MMBytes/MultiGeiger-V2/main/http_server.c

#include "http_server.h"

#include <stdlib.h>
#include <string.h>
#include <stdio.h>
#include <stdarg.h>
#include <time.h>
#include "esp_http_server.h"
#include "esp_log.h"
#include "esp_ota_ops.h"
#include "esp_partition.h"
#include "esp_chip_info.h"     // V2.3.13: chip-model lookup for OTA target validation
#include "esp_app_format.h"    // V2.3.13: ESP_CHIP_ID_* constants for OTA validation
#include "esp_app_desc.h"
#include "esp_flash.h"
#include "esp_heap_caps.h"
#include "esp_system.h"
#include "esp_timer.h"
#include "esp_wifi.h"
#include "esp_mac.h"
#include "esp_netif.h"
#include "esp_sntp.h"
#include "lwip/ip4_addr.h"
#include "lwip/sockets.h"
#include "lwip/inet.h"
#include "mbedtls/base64.h"
#include "esp_tls_errors.h"   // V2.8.0: ESP_TLS_ERR_SSL_WANT_READ/_WRITE — how
                              // a TLS recv timeout reaches update_post

#include "version.h"
#include "applog.h"
#include "diag.h"              // V2.4.32: diag_log_heap (net-RAM split at OTA-prep)
#include "coredump.h"          // V2.4.18: panic dump availability + summary + /coredump.elf
#include "hal.h"
#if HAL_HAS_PSRAM
#include "esp_psram.h"         // V2.8.2: esp_psram_get_size — the /status Memory line was a literal "8 MB"
#endif
#include "pm_sensor.h"
#include "env_sensor.h"
#include "noise_sensor.h"
#include "sgp41.h"             // V2.6.15: SGP41 VOC+NOx sensor (NOx index only)
#include "display.h"           // V2.3.30: live-apply OLED brightness via display_set_contrast
#include "als.h"               // V2.3.29: ambient light sensor (FeatherS3-D)
#include "veml7700.h"          // V2.3.30: I²C ambient light sensor (any board)
#include "fuel_gauge.h"        // V2.6.6: MAX17048 battery fuel gauge (FeatherS3-D)
#include "gnss.h"              // V2.5.8: I²C GNSS receiver (PA1010D / MAX-M10S)
#include "sd_logger.h"         // V2.6.19: standalone-mode CSV logger status (/status card)
#include "tube.h"
#include "tube_pcnt.h"         // V2.5.16: release PCNT comb DRAM in OTA teardown
#include "speaker.h"           // V2.7.5: silence the pulse tick in OTA teardown
#include "history.h"            // V2.5.6: CPM history for the /status graph
#include "transmission.h"
#include "log_ftp.h"
#include "main_status.h"       // V2.4.1 (A4): consolidated status snapshot
#include "mqtt.h"              // V2.4.4: MQTT connection state for /status row
#include "syslog.h"            // V2.4.15: tear down UDP socket in OTA teardown
#include "sysinfo.h"           // V2.4.26: reset_reason_str / chip_model_str (also used by mqtt.c)
#include "ntp.h"               // ntp_time_valid — the clock-sane gate
#include "util.h"              // V2.4.1+ (T1): ct_memcmp, html_esc, url_decode, safe_strcpy
#include "env_api.h"           // V2.7.3: /api/env wire contract (format + parse)
#include "lorawan.h"           // V2.6.23 (T8): lorawan_get_status()/_state_name()/_region_name()
                               // for /status; no-op stubs on the ten non-V4-R2 boards (see
                               // lorawan.h) so this include is unconditional like gnss.h/sgp41.h.
#include "tls_cert.h"          // V2.8.0: PEM pointers + fingerprint for HTTPS
#include "tls_logic.h"         // V2.8.0: https_redirect_location (Task 5)
#include "freertos/task.h"     // V2.8.0: uxTaskGetStackHighWaterMark — httpd stack headroom on /
#if HAL_HAS_HTTPS
#include "esp_https_server.h"  // V2.8.0: httpd_ssl_start — same httpd underneath, TLS on top
#endif
#if HAL_HAS_LORAWAN
#include "lorawan_codec.h"     // V2.6.23 (T8): lw_hex_decode() — /config POST EUI/key length
                               // validation, V4-R2 only. Ringfenced per the brief: other boards
                               // must not gain even this glue.
#endif

static const char *TAG = "http";

static httpd_handle_t s_server   = NULL;
#if HAL_HAS_HTTPS
// V2.8.0: true once httpd_ssl_start() succeeded on :443. Read by the :80
// instance bring-up (Task 5) and the /status Device card; false means we
// fell back to plain HTTP on :80 and there is nothing to redirect to.
static bool s_https_up = false;
// V2.8.0 (fix wave 5): https_enable as read at http_server_start(), before a
// /config POST can overwrite *s_cfg in place. The transport cannot change
// live, so the /status Device card must describe what THIS boot is doing,
// not a pending edit — read this instead of s_cfg->https_enable there.
static bool s_https_cfg_at_boot = false;
static httpd_handle_t s_redirect = NULL;   // :80 instance, NULL if not running
#endif
static config_t      *s_cfg      = NULL;
static const char    *s_chip_id  = "";
static char           s_mac_str[18] = "??:??:??:??:??:??";   // filled at start
// V2.4.1 (A9): the pre-V2.4.1 `static volatile bool s_restart_requested`
// + `http_server_restart_requested()` polled-flag pair was replaced with
// an event-bit notification — handlers now call main_request_restart()
// from main_status.h, which both sets a persistent flag and wakes the
// main loop's xEventGroupWaitBits via EV_RESTART. Drops "click Save and
// restart" -> reboot latency from up to 1 s to ~µs.

// --- Access log --------------------------------------------------------------
// Logs every incoming request with its URI and client IP. Called at the top of
// every handler, before auth checks, so unauthorised attempts are visible too.

static void peer_ipstr(httpd_req_t *req, char *out, size_t outsz) {
    if (outsz == 0) return;
    out[0] = '?';
    out[1] = 0;
    int sockfd = httpd_req_to_sockfd(req);
    if (sockfd < 0) return;
    struct sockaddr_storage addr;
    socklen_t len = sizeof(addr);
    if (getpeername(sockfd, (struct sockaddr *)&addr, &len) != 0) return;
    if (addr.ss_family == AF_INET) {
        inet_ntop(AF_INET,
                  &((struct sockaddr_in *)&addr)->sin_addr,
                  out, outsz);
    } else if (addr.ss_family == AF_INET6) {
        inet_ntop(AF_INET6,
                  &((struct sockaddr_in6 *)&addr)->sin6_addr,
                  out, outsz);
    }
}

#if HAL_HAS_HTTPS
static void tls_sess_mark_served(int fd);   // defined in the TLS session accounting block below
#endif
static void log_access(httpd_req_t *req, const char *what) {
    char ipstr[48];
    peer_ipstr(req, ipstr, sizeof(ipstr));
    ESP_LOGI(TAG, "%s from %s", what, ipstr);
#if HAL_HAS_HTTPS
    // Only the :443 instance has TLS sessions to account for; the :80
    // handlers share this helper but must not touch the table (single-task
    // rule, see the TLS session accounting block).
    if (req->handle == s_server) tls_sess_mark_served(httpd_req_to_sockfd(req));
#endif
}

#if HAL_HAS_HTTPS
// --- TLS session accounting (V2.8.1) ------------------------------------------
// A browser opens several connections to a new host at once; on this single
// httpd task each TLS handshake is ~1 s of software ECDSA (the S3 has no ECC
// block), so the spares wait their turn, COMPLETE the handshake, and are then
// reset by the client before sending a request (bench + five-node review,
// 2026-09-13; still the case with the CA imported into the browser, so it is
// ordinary speculative pre-connection, not a certificate-error retry).
// esp-tls logs each such first-read reset at ERROR
// ("read error :-0x0050"), two to five per page load, and that tag also
// carries every genuine TLS read/write failure — so it must stay at ERROR.
// Instead, account for sessions here: mark the socket at its first request,
// and at session close report the ones that never carried one at INFO. A
// "read error" that is NOT paired with a "closed before any request" line is
// the real thing.
//
// Both callbacks run on the :443 httpd task, and log_access() marks a
// session only when the request arrived on that instance (req->handle ==
// s_server) — the :80 handlers also call log_access() but never reach the
// table — so every access is from ONE task and it needs no lock.
#define TLS_SESS_SLOTS 8   // > max_open_sockets (5) + the accept in flight
static struct { int fd; bool served; } s_tls_sess[TLS_SESS_SLOTS];

static void tls_sess_mark_served(int fd) {
    for (int i = 0; i < TLS_SESS_SLOTS; i++) {
        if (s_tls_sess[i].fd == fd) { s_tls_sess[i].served = true; return; }
    }
}

static void tls_sess_user_cb(esp_https_server_user_cb_arg_t *arg) {
    int fd = -1;
    if (!arg || !arg->tls || esp_tls_get_conn_sockfd(arg->tls, &fd) != ESP_OK) return;
    switch (arg->user_cb_state) {
    case HTTPD_SSL_USER_CB_SESS_CREATE:
        for (int i = 0; i < TLS_SESS_SLOTS; i++) {
            if (s_tls_sess[i].fd == 0 || s_tls_sess[i].fd == fd) {
                s_tls_sess[i].fd = fd; s_tls_sess[i].served = false; return;
            }
        }
        return;                      // table full: this session goes unaccounted
    case HTTPD_SSL_USER_CB_SESS_ERROR:
        // Handshake never completed. This fires for EVERY failed handshake —
        // a browser hanging up mid-handshake (-0x7280, about once per cold
        // page load), but also a port scan, a plaintext probe on :443, a
        // version mismatch, or the 9 s handshake budget — and the callback
        // cannot tell them apart: httpd_ssl_open clears the esp-tls error
        // record before invoking it. So this line is a marker, not a verdict;
        // the code on the esp-tls line above it says which case. V2.8.2: name
        // the two codes an operator actually meets. The stress test of
        // 2026-09-15 showed a silent client logs
        // "esp_tls_create_server_session failed, 0xffff7ff7" — that is
        // -0x8009 = ESP_ERR_ESP_TLS_SERVER_HANDSHAKE_TIMEOUT, our 9 s
        // tls_handshake_timeout_ms — and the old text still blamed a browser.
        ESP_LOGI(TAG, "TLS handshake on fd %d did not complete — see the esp-tls line above "
                      "(-0x7280 = client hung up, a browser's spare connection; "
                      "0xffff7ff7 = the 9 s handshake budget, a client that never spoke)", fd);
        return;
    case HTTPD_SSL_USER_CB_SESS_CLOSE:
        for (int i = 0; i < TLS_SESS_SLOTS; i++) {
            if (s_tls_sess[i].fd == fd) {
                if (!s_tls_sess[i].served) {
                    ESP_LOGI(TAG, "TLS session on fd %d closed before any request "
                                  "(a browser's abandoned parallel connection — harmless)", fd);
                }
                s_tls_sess[i].fd = 0;
                return;
            }
        }
        return;
    default:
        return;
    }
}
#endif  // HAL_HAS_HTTPS

// --- Auth --------------------------------------------------------------------

// V2.4.1+ (T1): ct_memcmp moved to util.h as a static inline so the host-
// side test runner under `test/` can include it directly. Same constant-
// time semantics as the V2.3.33 (B2) original.

// Returns true if Authorization header is "Basic base64(admin:<ap_password>)".
// On failure, sends 401 + WWW-Authenticate and returns false. The caller must
// return ESP_OK immediately without sending anything further.
//
// Distinguishes two failure modes: header absent (expected first-touch from
// a fresh browser — logged as INFO) vs. header present but wrong credentials
// (a real bad-password attempt — logged as WARN so it stands out in /log).
static bool check_auth(httpd_req_t *req) {
    char header[160];
    size_t hlen = httpd_req_get_hdr_value_len(req, "Authorization");
    bool header_present = (hlen > 0 && hlen < sizeof(header));
    if (!header_present) goto unauth;
    if (httpd_req_get_hdr_value_str(req, "Authorization", header, sizeof(header)) != ESP_OK) {
        goto unauth;
    }
    if (strncmp(header, "Basic ", 6) != 0) goto unauth;

    char userpass[128];
    int n = snprintf(userpass, sizeof(userpass), "admin:%s", s_cfg->ap_password);
    if (n <= 0 || (size_t)n >= sizeof(userpass)) goto unauth;

    unsigned char expected[200];
    size_t enc_len = 0;
    if (mbedtls_base64_encode(expected, sizeof(expected) - 1, &enc_len,
                              (const unsigned char *)userpass, strlen(userpass)) != 0) {
        goto unauth;
    }
    expected[enc_len] = 0;
    // V2.3.33: length check first, then constant-time byte compare. Length
    // mismatch is non-secret (derivable from the credential layout) so the
    // early exit is fine; the byte comparison must be timing-safe.
    size_t got_len = strlen(header + 6);
    if (got_len != enc_len) goto unauth;
    if (ct_memcmp(header + 6, expected, enc_len) != 0) goto unauth;
    return true;

unauth:
    if (header_present) {
        char ipstr[48];
        peer_ipstr(req, ipstr, sizeof(ipstr));
        ESP_LOGW(TAG, "auth failed for %s from %s", req->uri, ipstr);
    }
    httpd_resp_set_status(req, "401 Unauthorized");
    httpd_resp_set_hdr(req, "WWW-Authenticate", "Basic realm=\"MultiGeiger\"");
    httpd_resp_send(req, NULL, 0);
    return false;
}

// --- CSRF guard for state-changing POST handlers ----------------------------
//
// V2.3.33: defends against cross-site request forgery on /config, /update,
// /reboot. Basic-auth credentials are cached per-origin by browsers and
// auto-attached to any subsequent request to the same origin — including
// cross-origin form POSTs from a malicious page the admin happens to visit
// in the same browser session. Without this guard, an attacker page can
// `<form action="http://device/config" method=POST>` with arbitrary fields,
// the browser attaches the cached Authorization header, and the request
// succeeds silently.
//
// Defence: require the request's Origin header to match this server's scheme
// AND Host (preferred — all modern browsers set Origin on cross-origin POST
// and on most same-origin POSTs); fall back to Referer, matched the same way
// on its host prefix. If neither header is present, deny — programmatic
// clients (curl, scripts) can pass `-H "Origin: http://<device>:<port>"`, or
// `-H "Origin: https://<device>"` on an HTTPS node, to satisfy the check.
//
// V2.8.0 (fix wave 7): the scheme is part of the comparison, not stripped and
// ignored. An origin is scheme+host+port, and with :80 still open (redirector,
// no HSTS) an attacker who answers port 80 — or spoofs it on the LAN — can
// serve a page from `http://<device>` whose form POSTs to `https://<device>`;
// a host-only check would call that same-origin, and the browser attaches the
// Basic credential it cached for :443. Binding the scheme the main server
// actually runs on closes that path.
//
// Caller must `return ESP_OK` immediately when this returns false.
static bool check_same_origin(httpd_req_t *req) {
    char host[64];
    if (httpd_req_get_hdr_value_str(req, "Host", host, sizeof(host)) != ESP_OK) {
        goto deny;
    }
    size_t host_len = strlen(host);
    // The transport this handler is reachable on. Protected POSTs only ever
    // land on the main instance: the :80 instance serves only /cert.pem, /log
    // and /api/env (none protected) plus the 301 wildcard, so there is no
    // mixed case to consider here.
#if HAL_HAS_HTTPS
    const char *scheme = s_https_up ? "https://" : "http://";
#else
    const char *scheme = "http://";
#endif
    size_t scheme_len = strlen(scheme);

    char origin[128];
    if (httpd_req_get_hdr_value_str(req, "Origin", origin, sizeof(origin)) == ESP_OK) {
        // Origin format: "scheme://host[:port]" with no path. The scheme must
        // be ours, and what follows it must equal Host exactly.
        if (strncmp(origin, scheme, scheme_len) != 0) goto deny;
        if (strcmp(origin + scheme_len, host) == 0) return true;
        goto deny;
    }

    char referer[160];
    if (httpd_req_get_hdr_value_str(req, "Referer", referer, sizeof(referer)) == ESP_OK) {
        // Referer format: "scheme://host[:port]/path?query#frag". Same scheme
        // rule, then the host portion (up to the first '/', '?', '#' or NUL
        // terminator) must equal Host.
        if (strncmp(referer, scheme, scheme_len) != 0) goto deny;
        const char *p = referer + scheme_len;
        if (strncmp(p, host, host_len) == 0) {
            char next = p[host_len];
            if (next == '/' || next == 0 || next == '?' || next == '#') {
                return true;
            }
        }
        goto deny;
    }

deny:
    {
        char ipstr[48];
        peer_ipstr(req, ipstr, sizeof(ipstr));
        ESP_LOGW(TAG, "CSRF check failed for POST %s from %s", req->uri, ipstr);
    }
    httpd_resp_set_status(req, "403 Forbidden");
    httpd_resp_set_type(req, "text/plain; charset=utf-8");
    httpd_resp_send(req, "Cross-origin POST refused (CSRF protection). "
                        "Submit from the device's own pages.",
                    HTTPD_RESP_USE_STRLEN);
    return false;
}

// --- Security response headers ----------------------------------------------
//
// V2.3.33: clickjacking protection for the admin UI. `DENY` blocks framing
// from any origin (the device never frames itself either). Applied to
// success responses on /config, /update, /reboot — the pages browsers
// actually render. Error responses funnelled through `httpd_resp_send_err`
// build their own minimal response and aren't normally framed in attacks.
static void set_security_headers(httpd_req_t *req) {
    httpd_resp_set_hdr(req, "X-Frame-Options", "DENY");
}

// --- HTML escape + URL decode + hex_nibble ----------------------------------
// V2.4.1+ (T1): moved to util.h as static inline so the host-side test
// runner under `test/` can include them directly. Same semantics as before
// (html_esc V2.0+, hex_nibble V2.0+, url_decode V2.4.1 B6 RFC-strict).

// V2.6.24: html_esc()'s TRUE worst case is 6 bytes out per byte in (every
// char -> "&quot;"), per its own doc in util.h. Every escape buffer in this
// file was historically sized to a ~3-4x convention (traceable to a V2.4.4
// comment that called "&amp;" the worst case), which made html_esc truncate
// metacharacter-dense values — and for /config that truncation is not just
// cosmetic: the form re-displays the shortened value and the next Save
// PERSISTS it back. Size every escape destination with ESC_WORST().
// V2.8.8: ESC_WORST moved to util.h, next to html_esc, so the host tests pin
// the exact macro these buffers use (see its comment there for the +2).

// --- GET / (status, no auth) -------------------------------------------------

// V2.5.33: format_uptime() moved to util.h (static inline) so transmission.c's
// heap-guard reboot log line can reuse the exact /status uptime formatting.

// Decode wifi_auth_mode_t to a short label. Names match what most APs use in
// their admin UI (the IDF enum names like AUTH_WPA2_PSK are too jargon-y).
static const char *wifi_auth_str(wifi_auth_mode_t m) {
    switch (m) {
        case WIFI_AUTH_OPEN:            return "Open";
        case WIFI_AUTH_WEP:             return "WEP";
        case WIFI_AUTH_WPA_PSK:         return "WPA-PSK";
        case WIFI_AUTH_WPA2_PSK:        return "WPA2-PSK";
        case WIFI_AUTH_WPA_WPA2_PSK:    return "WPA/WPA2-PSK";
        case WIFI_AUTH_WPA2_ENTERPRISE: return "WPA2-Enterprise";
        case WIFI_AUTH_WPA3_PSK:        return "WPA3-PSK";
        case WIFI_AUTH_WPA2_WPA3_PSK:   return "WPA2/WPA3-PSK";
        default:                        return "?";
    }
}

// Compact phy-mode summary like "bgn" or "ax". Each capability bit becomes a
// letter; absent radios just drop out (no padding). IDF 6.0 exposes 11a/ac/ax
// flags too — prepended with their own letters where relevant.
static void wifi_phy_str(const wifi_ap_record_t *ap, char *out, size_t sz) {
    char buf[16];
    int n = 0;
    if (ap->phy_11b)  buf[n++] = 'b';
    if (ap->phy_11g)  buf[n++] = 'g';
    if (ap->phy_11n)  buf[n++] = 'n';
    if (ap->phy_11a)  buf[n++] = 'a';
    if (ap->phy_11ac) { buf[n++] = 'a'; buf[n++] = 'c'; }
    if (ap->phy_11ax) { buf[n++] = 'a'; buf[n++] = 'x'; }
    if (ap->phy_lr)   buf[n++] = 'L';      // ESP-NOW long-range, rare
    buf[n] = 0;
    if (n == 0) snprintf(out, sz, "?");
    else        snprintf(out, sz, "%s", buf);
}

// --- Certificate line (V2.8.0; moved to the Network card in V2.8.1) -----------
// The certificate is bound to the network — its SAN names the STA address and
// it re-issues when that address changes — so it lives at the bottom of the
// Network card, after the address it certifies. Every Network branch (STA,
// AP-only, no connection) ends with it: an AP-only node serves the same
// certificate at 192.168.4.1.
//
// Five states, not three: a /config POST writes *s_cfg in place before the
// reboot that would act on it, so the live s_cfg->https_enable can disagree
// with what THIS boot is doing; s_https_cfg_at_boot is the value latched in
// http_server_start. The fingerprint is a 95-char token with no spaces, so
// it needs .fp (monospace + overflow-wrap:anywhere) to wrap inside the card
// instead of running past its edge (V2.8.1).
//
// Static return buffer: the whole page renders on the ONE :443 httpd task
// (see the CRITICAL note in http_server_start), same rule as every other
// scratch buffer in this file.
static const char *cert_status_html(void) {
#if HAL_HAS_HTTPS
    if (s_https_up && s_cfg->https_enable) {
        static char cert_line[192];
        snprintf(cert_line, sizeof(cert_line),
                 "SHA-256 <span class=\"fp\">%s</span> &middot; <a href=\"/cert.pem\">cert.pem</a>",
                 tls_cert_fingerprint());
        return cert_line;
    }
    if (s_https_up && !s_cfg->https_enable) {
        return "HTTPS on this boot; disabled in /config &mdash; plain HTTP after the next reboot";
    }
    if (!s_https_up && s_cfg->https_enable && !s_https_cfg_at_boot) {
        return "HTTPS enabled in /config &mdash; takes effect after the next reboot";
    }
    if (!s_https_up && !s_https_cfg_at_boot) {
        return "plain HTTP (HTTPS off in /config)";
    }
    // Wanted at boot (s_https_cfg_at_boot) but httpd_ssl_start failed — the
    // one genuine failure case, kept red.
    return "<span style=\"color:#c00\">plain HTTP — TLS start failed, see /log</span>";
#else
    return "plain HTTP (board has no PSRAM for a TLS server)";
#endif
}

static void format_net_info(char *out, size_t sz) {
    wifi_mode_t mode = WIFI_MODE_NULL;
    esp_wifi_get_mode(&mode);

    esp_netif_t *sta = esp_netif_get_handle_from_ifkey("WIFI_STA_DEF");
    wifi_ap_record_t ap;
    bool sta_up = (sta != NULL) && (esp_wifi_sta_get_ap_info(&ap) == ESP_OK);

    // ap_name is a user-editable config field, so escape it once for whichever
    // Network branch renders below — same treatment as the joined SSID
    // (ssid_esc) and the /config page. V2.6.24: sized ESC_WORST (was 96, which
    // truncated metacharacter-dense names) and static per the V2.4.22 pattern
    // (httpd runs all handlers on one thread) to keep it off the 8 KB stack.
    static char ap_name_esc[ESC_WORST(CFG_AP_NAME_MAX)];
    html_esc(s_cfg->ap_name, ap_name_esc, sizeof(ap_name_esc));

    // DHCP hostname (config wifi_hostname) — user-editable, so escaped like
    // ap_name above. Shown in both the STA and AP branches: main.c sets it on
    // both netifs before esp_wifi_start().
    static char host_esc[ESC_WORST(CFG_HOSTNAME_MAX)];
    html_esc(s_cfg->wifi_hostname, host_esc, sizeof(host_esc));

    if (sta_up) {
        esp_netif_ip_info_t ip = { 0 };
        esp_netif_get_ip_info(sta, &ip);
        esp_netif_dns_info_t d1 = { 0 }, d2 = { 0 };
        esp_netif_get_dns_info(sta, ESP_NETIF_DNS_MAIN,   &d1);
        esp_netif_get_dns_info(sta, ESP_NETIF_DNS_BACKUP, &d2);
        char ip_s[16], gw_s[16], nm_s[16], d1_s[16], d2_s[16];
        esp_ip4addr_ntoa(&ip.ip,      ip_s, sizeof(ip_s));
        esp_ip4addr_ntoa(&ip.gw,      gw_s, sizeof(gw_s));
        esp_ip4addr_ntoa(&ip.netmask, nm_s, sizeof(nm_s));
        esp_ip4addr_ntoa(&d1.ip.u_addr.ip4, d1_s, sizeof(d1_s));
        esp_ip4addr_ntoa(&d2.ip.u_addr.ip4, d2_s, sizeof(d2_s));
        bool has_d2 = (d2.ip.u_addr.ip4.addr != 0) &&
                      (d2.ip.u_addr.ip4.addr != d1.ip.u_addr.ip4.addr);
        // SSID is up to 32 bytes; the escape buffer takes the full 6x worst
        // case (V2.6.24, was 66 which truncated quote-heavy joined SSIDs —
        // this one isn't even our own config, it's whatever AP we joined).
        // static per the V2.4.22 single-threaded-httpd pattern.
        static char ssid_esc[ESC_WORST(32)];
        char ssid_raw[33] = {0};
        memcpy(ssid_raw, ap.ssid, sizeof(ap.ssid));
        ssid_raw[32] = 0;
        html_esc(ssid_raw, ssid_esc, sizeof(ssid_esc));
        char phy[8];
        wifi_phy_str(&ap, phy, sizeof(phy));
        const char *bw = (ap.second == WIFI_SECOND_CHAN_NONE) ? "BW20" : "BW40";
        // AID lives in a separate API in IDF 6.0 (was a wifi_ap_record_t
        // member in 5.x). 0 = not associated / unknown.
        uint16_t aid = 0;
        esp_wifi_sta_get_aid(&aid);
        main_status_t st;
        main_status_snapshot(&st);
        snprintf(out, sz,
                 "<div class=\"info\"><h3>Network</h3>"
                 // AP SSID = this device's own fallback/AP-mode SSID (config
                 // ap_name); distinct from the "SSID:" below = the network it's
                 // joined to. Lives in the Network block (moved out of System).
                 "<b>AP SSID:</b> %s<br>"
                 "<b>SSID:</b> %s<br>"
                 "<b>Security:</b> %s &middot; PHY %s &middot; %s &middot; channel %d<br>"
                 "<b>BSSID:</b> %02x:%02x:%02x:%02x:%02x:%02x &nbsp; AID %u<br>"
                 "<b>RSSI:</b> %d dBm<br>"
                 "<b>Hostname:</b> %s<br>"
                 "<b>IP:</b> %s<br>"
                 "<b>Gateway:</b> %s<br>"
                 "<b>Network Mask:</b> %s<br>"
                 "<b>DNS:</b> %s%s%s<br>"
                 "<b>Reconnects:</b> %lu since boot<br>"
                 "<b>Certificate:</b> %s"
                 "</div>",
                 ap_name_esc,
                 ssid_esc,
                 wifi_auth_str(ap.authmode), phy, bw, (int)ap.primary,
                 ap.bssid[0], ap.bssid[1], ap.bssid[2],
                 ap.bssid[3], ap.bssid[4], ap.bssid[5],
                 (unsigned)aid,
                 (int)ap.rssi,
                 host_esc,
                 ip_s, gw_s, nm_s,
                 d1_s, has_d2 ? ", " : "", has_d2 ? d2_s : "",
                 (unsigned long)st.reconnects,
                 cert_status_html());
        return;
    }

    if (mode == WIFI_MODE_AP || mode == WIFI_MODE_APSTA) {
        esp_netif_t *apn = esp_netif_get_handle_from_ifkey("WIFI_AP_DEF");
        esp_netif_ip_info_t ip = { 0 };
        if (apn) esp_netif_get_ip_info(apn, &ip);
        char ip_s[16];
        esp_ip4addr_ntoa(&ip.ip, ip_s, sizeof(ip_s));
        snprintf(out, sz, "<div class=\"info\"><h3>Network</h3><b>AP SSID:</b> %s<br><b>Hostname:</b> %s<br><b>IP:</b> %s (AP mode)<br><b>Certificate:</b> %s</div>",
                 ap_name_esc, host_esc, ip_s, cert_status_html());
        return;
    }

    snprintf(out, sz, "<div class=\"info\"><h3>Network</h3><b>Network:</b> No connection<br><b>Certificate:</b> %s</div>",
             cert_status_html());
}

// --- Device identity block ---------------------------------------------------
// All format_* helpers emit a complete self-wrapping <div class="info"> block
// so status_get can stream them sequentially via httpd_resp_send_chunk without
// needing a top-level body buffer. Empty output (e.g. tube disabled, no env
// sensor) is a single null terminator — the caller's strlen() sees 0, the
// chunk is skipped.
static void format_device(char *out, size_t sz) {
    esp_chip_info_t chip;
    esp_chip_info(&chip);
    uint32_t flash_size = 0;
    esp_flash_get_size(NULL, &flash_size);
    const char *model = chip_model_str(chip.model);
    char feat[32]; feat[0] = 0;
    if (chip.features & CHIP_FEATURE_WIFI_BGN) strncat(feat, "WiFi ", sizeof(feat)-strlen(feat)-1);
    if (chip.features & CHIP_FEATURE_BLE)      strncat(feat, "BLE ",  sizeof(feat)-strlen(feat)-1);
    if (chip.features & CHIP_FEATURE_BT)       strncat(feat, "BT ",   sizeof(feat)-strlen(feat)-1);
    bool emb_flash = (chip.features & CHIP_FEATURE_EMB_FLASH) != 0;
    bool emb_psram = (chip.features & CHIP_FEATURE_EMB_PSRAM) != 0;
    if (emb_flash) strncat(feat, "EmbFlash ", sizeof(feat)-strlen(feat)-1);
    if (emb_psram) strncat(feat, "EmbPSRAM ", sizeof(feat)-strlen(feat)-1);
    // Strip trailing space.
    size_t fl = strlen(feat); if (fl && feat[fl-1] == ' ') feat[fl-1] = 0;

    const esp_app_desc_t *app = esp_app_get_description();
    const char *fw_date = app ? app->date : __DATE__;
    const char *fw_time = app ? app->time : __TIME__;

#if HAL_HAS_ANTENNA_SWITCH
    const char *antenna = s_cfg->use_external_antenna ? "EXTERNAL u.FL" : "internal PCB";
#else
    const char *antenna = "(N/A — internal only)";
#endif

    // V2.8.2: report the PSRAM the chip actually found, not a literal. The
    // string was hard-coded "8 MB" for every HAL_HAS_PSRAM board and so lied on
    // the six 2 MB boards (QT Py PICO, Heltec V4-R2, SparkFun Thing Plus S3,
    // TFT Feather, Feather V2, Feather S3 4MB/2MB); only FeatherS3-D, XIAO S3
    // and SparkFun C5 truly have 8 MB. Same call applog.c uses for its boot
    // line. Reads 0 if PSRAM init failed — honest, unlike the old literal.
#if HAL_HAS_PSRAM
    char psram[32];
    snprintf(psram, sizeof(psram), " &middot; %u MB PSRAM",
             (unsigned)(esp_psram_get_size() / (1024 * 1024)));
#else
    const char *psram = "";      // no PSRAM line at all on internal-RAM-only boards
#endif

    snprintf(out, sz,
        "<div class=\"info\"><h3>Device</h3>"
        "<b>Chip ID:</b> %s<br>"
        "<b>MAC:</b> %s<br>"
        "<b>Board:</b> %s<br>"
        "<b>Chip:</b> %s rev v%d.%d &middot; %d cores &middot; %s<br>"
        "<b>Memory:</b> %lu MB flash%s<br>"
        "<b>Firmware:</b> %s &nbsp; (built %s %s)<br>"
        "<b>Antenna:</b> %s"
        "</div>",
        s_chip_id,
        s_mac_str,
        BOARD_NAME,
        model, chip.revision / 100, chip.revision % 100, chip.cores, feat[0] ? feat : "?",
        (unsigned long)(flash_size / (1024 * 1024)),
        psram,
        VERSION_STR, fw_date, fw_time,
        antenna);
}

// --- System block ------------------------------------------------------------
// Uptime, reset reason, heap, NTP last-sync.
static void format_ago(int64_t now_unix, int64_t past_unix, char *out, size_t sz) {
    if (past_unix <= 0 || now_unix < past_unix) { snprintf(out, sz, "never"); return; }
    long s = (long)(now_unix - past_unix);
    if (s < 60)        snprintf(out, sz, "%lds ago", s);
    else if (s < 3600) snprintf(out, sz, "%ldm %lds ago", s / 60, s % 60);
    else if (s < 86400)snprintf(out, sz, "%ldh %ldm ago", s / 3600, (s / 60) % 60);
    else               snprintf(out, sz, "%ldd %ldh ago", s / 86400, (s / 3600) % 24);
}

static void format_wallclock(int64_t unix_t, char *out, size_t sz) {
    if (unix_t <= 0) { snprintf(out, sz, "—"); return; }
    time_t t = (time_t)unix_t;
    struct tm tm;
    localtime_r(&t, &tm);
    strftime(out, sz, "%Y-%m-%d %H:%M:%S", &tm);
}

static void format_system(char *out, size_t sz, unsigned long uptime_s, time_t now_wall) {
    uint32_t free_heap = esp_get_free_heap_size();
    uint32_t min_free  = esp_get_minimum_free_heap_size();
    uint32_t max_alloc = heap_caps_get_largest_free_block(MALLOC_CAP_8BIT);
    char uptime_buf[32];
    format_uptime(uptime_s, uptime_buf, sizeof(uptime_buf));

    // NTP last-sync. sntp_get_sync_status() returns COMPLETED briefly after
    // each callback then resets to RESET — which is misleading on a page that
    // refreshes infrequently. Better: just check whether the wall clock looks
    // sane (same predicate ntp_time_valid uses) and show the most recent
    // localtime sample.
    // now_wall is captured once in status_get so "clock now" and "Started+Uptime"
    // are rooted in the same timestamp — their arithmetic is always consistent.
    char ntp_line[96];
    if (ntp_time_valid()) {     // clock is real (NTP-synced or sane RTC carry-over)
        char ts[24];
        format_wallclock((int64_t)now_wall, ts, sizeof(ts));
        snprintf(ntp_line, sizeof(ntp_line), "synced &middot; clock now %s", ts);
    } else {
        snprintf(ntp_line, sizeof(ntp_line), "<span style='color:#c80'>not synced yet</span>");
    }

    // V2.5.22: append the boot wall-clock to the Uptime line. Boot epoch is
    // captured once at first NTP sync (ntp_boot_epoch()) so it never drifts:
    // recomputing now-uptime on every page load walks ~1s per few hours because
    // esp_timer counts raw crystal ticks while time(NULL) is NTP-slewed.
    char started_suffix[48] = "";
    time_t boot_epoch = ntp_boot_epoch();
    if (boot_epoch) {
        char started[24];
        format_wallclock((int64_t)boot_epoch, started, sizeof(started));
        snprintf(started_suffix, sizeof(started_suffix), " (Started %s)", started);
    }

    // V2.4.18: core dump line. Three render modes:
    //   - no dump:  "none"
    //   - dump:     "yes &middot; <SZ> bytes &middot; task=<NAME> PC=0x...
    //                <reason> [download] [erase]"
    // The download link is always shown when a dump exists; the erase
    // button submits via a tiny form to /coredump_erase (CSRF-checked
    // POST) and reloads.
    // V2.4.22: cd_summary[320] + cd_line[640] = ~960 B moved from stack
    // to BSS. Same V2.4.20 fix pattern — large buffers on the httpd task's
    // 8 KB stack are fragile, and format_system is called from the `/`
    // handler which already pays the static-ified buf[1600] tax. Safe
    // because esp_http_server uses a single thread (httpd_thread runs all
    // URI handlers serially via select), so format_system is never
    // re-entered. Both branches of the if/else below always populate
    // cd_line before it's read, so no per-call zero-init needed.
    static char cd_summary[320];
    coredump_get_summary_html(cd_summary, sizeof(cd_summary));
    static char cd_line[640];
    if (coredump_have_dump()) {
        // Inline form for the erase button keeps the System block
        // self-contained — no JS, no separate page. The hidden submit
        // POSTs to /coredump_erase with same-origin so the CSRF check
        // succeeds; basic-auth is auto-attached by the browser since
        // the user already authenticated for /status.
        snprintf(cd_line, sizeof(cd_line),
            "<b>Core dump:</b> %s &middot; "
            "<a href=\"/coredump.elf\">download .elf</a> &middot; "
            "<form method=\"POST\" action=\"/coredump_erase\" "
            "style=\"display:inline\" "
            "onsubmit=\"return confirm('Erase core dump?');\">"
            "<button type=\"submit\">erase</button></form><br>",
            cd_summary);
    } else {
        snprintf(cd_line, sizeof(cd_line),
                 "<b>Core dump:</b> %s<br>", cd_summary);
    }

    // V2.4.28: I²C sensor-read-error counter. Climbs when env / PM / noise /
    // light reads fail at the top-level call site in do_tx_cycle. A
    // monotonically rising value points at marginal supply, flaky bus, or
    // a failing sensor — pair it with `reset_reason: BROWNOUT` to confirm
    // power vs bus suspicion.
    main_status_t st;
    main_status_snapshot(&st);

    // V2.8.0: this handler runs ON the httpd task, so the high-water mark
    // read here is the httpd task's own — after TLS handshakes on HTTPS
    // boards, which run on this task before any handler. Below ~1 KB means
    // the stack_size in http_server_start needs raising.
    const unsigned httpd_stack_free = (unsigned)uxTaskGetStackHighWaterMark(NULL) * sizeof(StackType_t);

    snprintf(out, sz,
             "<div class=\"info\"><h3>System</h3>"
             "<b>Uptime:</b> %s%s<br>"
             "<b>Reset reason:</b> %s<br>"
             "%s"   // core-dump line (V2.4.18)
             "<b>Free heap:</b> %lu bytes<br>"
             "<b>Min free heap:</b> %lu bytes<br>"
             "<b>Max allocation:</b> %lu bytes<br>"
             "<b>httpd stack headroom:</b> %u bytes<br>"
             "<b>I²C errors:</b> %lu since boot<br>"
             "<b>NTP:</b> %s<br>"
             // V2.4.9: resolved display layout mode. Shows what display.c
             // picked at boot (e.g. "auto (resolved: rotation)" or
             // "radiation (forced)") so the user can confirm the runtime
             // decision without digging into /log.
             "<b>Display layout:</b> %s<br>"
             // V2.6.30: attached panel identity (probe result, e.g. "SerLCD
             // 20x4 @0x72"), so a fleet sweep over /status answers "which
             // display is on this node" without serial access to the boot log.
             "<b>Display hardware:</b> %s"
             "</div>",
             uptime_buf, started_suffix,
             reset_reason_str(esp_reset_reason()),
             cd_line,
             (unsigned long)free_heap,
             (unsigned long)min_free,
             (unsigned long)max_alloc,
             httpd_stack_free,
             (unsigned long)st.i2c_errors,
             ntp_line,
             display_mode_str(),
             display_backend_str());
}

// --- Cycle block -------------------------------------------------------------
static void format_cycle(char *out, size_t sz, unsigned long uptime_ms) {
    main_status_t st;
    main_status_snapshot(&st);

    char wall[32], ago[24];
    format_wallclock(st.last_cycle_at, wall, sizeof(wall));
    format_ago((int64_t)time(NULL), st.last_cycle_at, ago, sizeof(ago));

    // Next cycle = last + tx_interval. If we haven't run yet, "—".
    char next_line[64];
    if (st.last_cycle_ms == 0) {
        snprintf(next_line, sizeof(next_line), "—");
    } else {
        long remaining_ms = (long)(st.last_cycle_ms + s_cfg->tx_interval_ms) - (long)uptime_ms;
        if (remaining_ms < 0) remaining_ms = 0;
        snprintf(next_line, sizeof(next_line), "in %lds", remaining_ms / 1000);
    }

    snprintf(out, sz,
        "<div class=\"info\"><h3>Cycle</h3>"
        "<b>Cycle #:</b> %lu<br>"
        "<b>Last dt:</b> %lu ms<br>"
        "<b>Interval:</b> %lu ms<br>"
        "<b>Last cycle:</b> %s &nbsp; (%s)<br>"
        "<b>Next cycle:</b> %s"
        "</div>",
        (unsigned long)st.cycles,
        (unsigned long)st.last_dt_ms,
        (unsigned long)s_cfg->tx_interval_ms,
        wall, ago,
        next_line);
}

// --- Radiation block (only when tube is enabled) -----------------------------
static void format_radiation(char *out, size_t sz) {
    if (!tube_is_enabled()) { out[0] = 0; return; }

    main_status_t st;
    main_status_snapshot(&st);

    // HV pulses per minute over the last cycle window. dt_ms == 0 means no
    // cycle has run yet; show a dash so we don't divide by zero. V2.4.27:
    // uses `last_hv_pulses_delta` (per-cycle) instead of `last_hv_pulses`
    // (cumulative-since-boot) — the previous form divided the cumulative
    // counter by one cycle's duration, producing a number that grew
    // unboundedly with uptime instead of the intended pulses/min rate.
    char hv_line[64];
    if (st.last_dt_ms > 0) {
        float hv_per_min = (float)st.last_hv_pulses_delta * 60000.0f / (float)st.last_dt_ms;
        snprintf(hv_line, sizeof(hv_line), "%.1f / min  (cumulative %lu)",
                 hv_per_min, (unsigned long)st.last_hv_pulses);
    } else {
        snprintf(hv_line, sizeof(hv_line), "—  (cumulative %lu)",
                 (unsigned long)st.last_hv_pulses);
    }

    // V2.5.16: width-filter indicator — only shown when the filter is active.
    // Makes it obvious on the page that the CPM above is POST-filter, and what
    // the pre-filter value was, so the effect is visible without the syslog.
    char filt_line[128];
    if (st.pcnt_filtering) {
        snprintf(filt_line, sizeof(filt_line),
                 "<b>PCNT width filter:</b> ON @%lu ns &mdash; raw CPM %lu "
                 "&rarr; filtered %lu<br>",
                 (unsigned long)st.pcnt_filter_width_ns,
                 (unsigned long)st.last_cpm_raw, (unsigned long)st.last_cpm);
    } else {
        filt_line[0] = 0;
    }

    snprintf(out, sz,
        "<div class=\"info\"><h3>Radiation</h3>"
        "<b>Tube:</b> enabled &middot; %s%s<br>"
        "<b>CPM:</b> %lu<br>"
        "%s"
        "<b>Dose rate:</b> %.3f µSv/h<br>"
        "<b>HV pulses:</b> %s"
        "</div>",
        tube_type_name(s_cfg->tube_type),   // V2.6.1: show the selected tube
        st.last_hv_error ? " &middot; <span style='color:#c00;font-weight:bold'>HV ERROR</span>" : "",
        (unsigned long)st.last_cpm, filt_line, st.last_usvph,
        hv_line);
}

// --- Environment block -------------------------------------------------------
static void format_environment(char *out, size_t sz) {
    if (!env_sensor_present()) { out[0] = 0; return; }
    main_status_t st;
    main_status_snapshot(&st);
    if (!st.have_env) {
        snprintf(out, sz,
            "<div class=\"info\"><h3>Environment</h3>"
            "<b>Sensor:</b> %s<br>"
            "awaiting first cycle..."
            "</div>", env_sensor_name());
        return;
    }
    snprintf(out, sz,
        "<div class=\"info\"><h3>Environment</h3>"
        "<b>Sensor:</b> %s<br>"
        "<b>Temperature:</b> %.2f °C<br>"
        "<b>Humidity:</b> %.2f %%<br>"
        "<b>Pressure:</b> %.2f hPa"
        "</div>",
        env_sensor_name(),
        st.env_t,
        st.env_h,
        st.env_p / 100.0f);
}

// Defensive append helper — defined below near format_uploads; forward-declared
// here so the multi-segment formatters above it (ALS / GNSS / PM) can use the
// clamped accumulation instead of bare `n += snprintf` (V2.5.20 review R4:
// on truncation the bare pattern pushes n past sz and `sz - n` underflows).
__attribute__((format(printf, 4, 5)))
static int append_safe(char *out, size_t sz, int n, const char *fmt, ...);

// --- Ambient light block ----------------------------------------------------
// Two possible sources, both shown when present:
//   * VEML7700 (I²C, any board, fixed 0x10) — accurate lux + raw ALS + white
//   * ALS-PT19 (FeatherS3-D analog, GPIO 4) — rough lux from voltage divider
//
// Reads happen on every /status request — VEML7700 is two short I²C reads
// (~1 ms total at 400 kHz), ALS-PT19 is a ~10 µs ADC oneshot. Fresh data
// for a page that's only loaded when the user opens it. The whole block
// is skipped if neither sensor is present.
static void format_als(char *out, size_t sz) {
    bool have_veml = veml7700_present();
    bool have_pt19 = als_present();
    if (!have_veml && !have_pt19) { out[0] = 0; return; }

    int n = append_safe(out, sz, 0, "<div class=\"info\"><h3>Ambient light</h3>");

    if (have_veml) {
        uint16_t als_raw = 0, white_raw = 0;
        float    lux = 0.0f;
        if (veml7700_read(&als_raw, &white_raw, &lux) == ESP_OK) {
            n = append_safe(out, sz, n,
                "<b>Sensor:</b> VEML7700 (I²C, 0x10)<br>"
                "<b>Reading:</b> %.1f lux (raw ALS=%u, white=%u, %s)",
                (double)lux, (unsigned)als_raw, (unsigned)white_raw,
                als_brightness_label(lux));
        } else {
            n = append_safe(out, sz, n,
                "<b>Sensor:</b> VEML7700 (I²C, 0x10)<br>read failed");
        }
        if (have_pt19) n = append_safe(out, sz, n, "<br><br>");
    }

    if (have_pt19) {
        uint32_t mv = 0;
        float    lux = 0.0f;
        if (als_read(NULL, &mv, &lux) == ESP_OK) {
            n = append_safe(out, sz, n,
                "<b>Sensor:</b> ALS-PT19 (analog, GPIO 4)<br>"
                "<b>Reading:</b> %lu mV (~%d lux, %s)",
                (unsigned long)mv, (int)lux, als_brightness_label(lux));
        } else {
            n = append_safe(out, sz, n,
                "<b>Sensor:</b> ALS-PT19 (analog, GPIO 4)<br>read failed");
        }
    }

    append_safe(out, sz, n, "</div>");
}

// --- Battery (MAX17048 fuel gauge, FeatherS3-D only) -----------------------
// V2.6.6: presence is the user-set `batt_present` config bool (see
// fuel_gauge.h for why VCELL alone can't auto-detect this), so this block
// is simply absent on every other board and on a FeatherS3-D where the user
// hasn't ticked "Battery attached". Read happens on every /status request,
// same cost class as the ambient-light block above it.
static void format_battery(char *out, size_t sz) {
    if (!fuel_gauge_present()) { out[0] = 0; return; }

    float volts = 0.0f, soc = 0.0f, rate = 0.0f;
    if (fuel_gauge_read(&volts, &soc, &rate) != ESP_OK) {
        int n = append_safe(out, sz, 0, "<div class=\"info\"><h3>Battery</h3>");
        append_safe(out, sz, n, "<b>Sensor:</b> MAX17048 (I²C, 0x36)<br>read failed</div>");
        return;
    }

    int n = append_safe(out, sz, 0, "<div class=\"info\"><h3>Battery</h3>");
    n = append_safe(out, sz, n,
        "<b>Sensor:</b> MAX17048 (I²C, 0x36)<br>"
        "<b>Voltage:</b> %.3f V<br>"
        "<b>Charge:</b> %.1f %%<br>"
        "<b>Rate:</b> %+.2f %%/hr (%s)",
        (double)volts, (double)soc, (double)rate,
        rate > 0.0f ? "charging" : (rate < 0.0f ? "discharging" : "idle"));
    append_safe(out, sz, n, "</div>");
}

// --- GNSS / position block --------------------------------------------------
// V2.5.8: shown only when a GNSS receiver was auto-detected at boot. Reads the
// cached fix snapshot — no I²C here; the receiver is drained on the main
// service task. Until the first valid fix we show the acquisition state
// (satellite count climbs as the receiver locks on).
static void format_gnss(char *out, size_t sz) {
    if (!gnss_present()) { out[0] = 0; return; }

    gnss_fix_t f;
    gnss_get_fix(&f);

    int n = append_safe(out, sz, 0,
        "<div class=\"info\"><h3>GNSS / Position</h3>"
        "<b>Sensor:</b> %s (I²C, 0x%02X)<br>",
        gnss_chip_name(), gnss_i2c_addr());

    // Unique chip ID — MAX-M10S only (UBX-SEC-UNIQID); empty for the PA1010D.
    const char *serial = gnss_serial();
    if (serial[0]) {
        n = append_safe(out, sz, n, "<b>Serial:</b> 0x%s<br>", serial);
    }

    if (!f.valid) {
        n = append_safe(out, sz, n,
            "<b>Fix:</b> acquiring… (%u satellites visible)", (unsigned)f.sats);
    } else {
        char utc[32] = "—";
        if (f.utc > 0) {
            struct tm tm_utc;
            gmtime_r(&f.utc, &tm_utc);
            strftime(utc, sizeof(utc), "%Y-%m-%dT%H:%M:%SZ", &tm_utc);
        }
        n = append_safe(out, sz, n,
            "<b>Fix:</b> %s, %u satellites, HDOP %.1f<br>"
            "<b>Position:</b> %.6f, %.6f "
            "(<a href=\"https://www.openstreetmap.org/?mlat=%.6f&amp;mlon=%.6f"
            "#map=15/%.6f/%.6f\" target=\"_blank\" rel=\"noopener\">map</a>)<br>"
            "<b>Altitude:</b> %.0f m MSL<br>"
            "<b>UTC:</b> %s",
            f.fix_3d ? "3D" : "2D", (unsigned)f.sats, (double)f.hdop,
            f.lat, f.lon, f.lat, f.lon, f.lat, f.lon,
            (double)f.alt_m, utc);
    }

    // V2.5.11: no "system time source" line — GNSS no longer sets the clock
    // (NTP is the sole source). The UTC above is the receiver's reported time.
    append_safe(out, sz, n, "</div>");
}

// --- SD logger block (standalone mode) --------------------------------------
// V2.6.19: standalone-mode CSV logging status (design spec §7). Board- AND
// mode-gated: sd_logger_get_status() only ever has real data on
// HAL_HAS_SD_CARD boards with standalone_sd ticked — everywhere else the
// fields sit at their zero/empty init forever (sd_logger.h), so showing the
// card there would just be permanent, misleading clutter. This is the only
// place a field node without a permanent AP can see logging health without
// pulling the card; a dedicated OLED page is deliberately deferred (spec §7).
#if HAL_HAS_SD_CARD
static void format_sd_logger(char *out, size_t sz) {
    if (!s_cfg->standalone_sd) { out[0] = 0; return; }

    sd_logger_status_t sd;
    sd_logger_get_status(&sd);

    int n = append_safe(out, sz, 0,
        "<div class=\"info\"><h3>SD Logger</h3>"
        "<b>SD card:</b> %s<br>",
        sd.mounted ? "mounted" : "NOT MOUNTED");

    if (sd.filename[0]) {
        // Device-generated (chip-id + UTC timestamp, sd_logger.h) — same
        // no-escape treatment as the GNSS serial/chip-id strings above,
        // not user-supplied config text.
        n = append_safe(out, sz, n, "<b>CSV file:</b> %s<br>", sd.filename);
    } else if (sd.mounted) {
        // File creation waits for the first GNSS clock sync (sd_logger.h) —
        // an empty name while mounted means "no fix yet", not a fault.
        n = append_safe(out, sz, n,
            "<b>CSV file:</b> &mdash; (waiting for GPS fix)<br>");
    }

    n = append_safe(out, sz, n,
        "<b>Rows written:</b> %lu", (unsigned long)sd.rows_written);

    if (sd.last_err != 0) {
        // V2.6.22 (M2): the two error domains sd_logger mixes into last_err
        // render differently — one bare %d showed ESP_ERR_TIMEOUT (0x107)
        // as a baffling "263" that reads like an errno.
        if (sd.last_err_is_esp) {
            n = append_safe(out, sz, n,
                "<br><b>Last error:</b> %s (streak %lu)",
                esp_err_to_name(sd.last_err), (unsigned long)sd.fail_streak);
        } else {
            n = append_safe(out, sz, n,
                "<br><b>Last error:</b> errno %d (%s) (streak %lu)",
                sd.last_err, strerror(sd.last_err),
                (unsigned long)sd.fail_streak);
        }
    }

    append_safe(out, sz, n, "</div>");
}
#endif

// --- Noise block -------------------------------------------------------------
static void format_noise(char *out, size_t sz) {
    if (!noise_sensor_present()) { out[0] = 0; return; }
    noise_sample_t n;
    if (noise_sensor_get_last_sample(&n) != ESP_OK) {
        snprintf(out, sz,
            "<div class=\"info\"><h3>Noise</h3>"
            "<b>Sensor:</b> %s<br>"
            "first window still integrating..."
            "</div>", noise_sensor_name());
        return;
    }
    snprintf(out, sz,
        "<div class=\"info\"><h3>Noise</h3>"
        "<b>Sensor:</b> %s (%s)<br>"
        "<b>LAeq:</b> %.1f dB(A)<br>"
        "<b>LA min / max:</b> %.1f / %.1f dB(A)"
        "</div>",
        noise_sensor_name(), noise_sensor_version(),
        n.laeq, n.la_min, n.la_max);
}

// --- SGP41 gas (NOx) block -----------------------------------------------
static void format_sgp41(char *out, size_t sz) {
    if (!sgp41_present()) { out[0] = 0; return; }
    int32_t nox_index;
    if (sgp41_get_nox_index(&nox_index) != ESP_OK) {
        // V2.6.15: distinguish first-boot warmup from a sensor that was
        // working and has since gone unresponsive (age-based cache
        // staleness in sgp41_get_nox_index()) — a fixed wording would
        // mislead hours/days into uptime.
        snprintf(out, sz,
            "<div class=\"info\"><h3>Gas (SGP41)</h3>%s"
            "</div>",
            sgp41_had_valid_reading() ? "sensor unresponsive"
                                       : "conditioning / warming up...");
        return;
    }
    snprintf(out, sz,
        "<div class=\"info\"><h3>Gas (SGP41)</h3>"
        "<b>NOx index:</b> %ld"
        "</div>",
        (long)nox_index);
}

// --- MQTT block --------------------------------------------------------------
//
// V2.4.4 (Phase 3): /status row for the MQTT client added in V2.4.2. Skipped
// when the user hasn't enabled MQTT — keeps the page tight on Madavi-only
// devices. Reads only from mqtt.c's connect-state flag + publish counter,
// never touches the broker from this HTTP-handler context (no I/O blocking).
static void format_mqtt(char *out, size_t sz) {
    if (!s_cfg->mqtt_enable) { out[0] = 0; return; }

    const bool connected = mqtt_is_connected();
    const uint32_t pubs  = mqtt_publish_count();
    // V2.8.5: a client that mqtt_init() refused to start (today: TLS Mode B
    // with no CA certificate) says WHY instead of a bare "disconnected".
    const char *cfg_err = mqtt_config_error();
    static char state_err[160];
    if (cfg_err) {
        snprintf(state_err, sizeof(state_err),
                 "<span style='color:#c00'>not started &mdash; %s</span>", cfg_err);
    }
    const char *state_html = cfg_err ? state_err
        : connected
        ? "<span style='color:#080'>connected</span>"
        : "<span style='color:#c00'>disconnected</span>";
    // V2.8.5: broker and topic prefix are user-entered config strings, so
    // they are HTML-escaped like ap_name / wifi_hostname on this page (they
    // went in raw before — a `<` or `"` in either broke the page). Static,
    // not stack, per the V2.4.22 pattern: all handlers share one 8 KB task.
    static char broker_esc[ESC_WORST(CFG_MQTT_HOST_MAX)];
    static char prefix_esc[ESC_WORST(CFG_MQTT_PFX_MAX)];
    html_esc(s_cfg->mqtt_broker,       broker_esc, sizeof(broker_esc));
    html_esc(s_cfg->mqtt_topic_prefix, prefix_esc, sizeof(prefix_esc));
    const char *broker_html = (s_cfg->mqtt_broker[0])
        ? broker_esc
        : "<i>(not set)</i>";

    // V2.4.6: TLS status row. Compact one-liner — full config lives on /config.
    const char *tls_html;
    if (!s_cfg->mqtt_tls_enable) {
        tls_html = "<span style='color:#888'>off (plain MQTT)</span>";
    } else {
        switch (s_cfg->mqtt_tls_mode) {
            case 0:  tls_html = "<span style='color:#080'>on &mdash; Mode A (Mozilla CA bundle)</span>"; break;
            case 1:  tls_html = s_cfg->mqtt_tls_ca[0]
                         ? "<span style='color:#080'>on &mdash; Mode B (custom CA cert)</span>"
                         : "<span style='color:#c00'>on &mdash; Mode B, but no CA cert configured</span>";
                     break;
            case 2:  tls_html = "<span style='color:#c80'>on &mdash; Mode D (skip verification)</span>"; break;
            default: tls_html = "<span style='color:#c00'>on &mdash; unknown mode</span>";              break;
        }
    }

    snprintf(out, sz,
        "<div class=\"info\"><h3>MQTT</h3>"
        "<b>Broker:</b> %s:%lu<br>"
        "<b>State:</b> %s<br>"
        "<b>Publishes since boot:</b> %lu<br>"
        "<b>Topic prefix:</b> <code>%s</code><br>"
        "<b>HA Discovery:</b> %s<br>"
        "<b>TLS:</b> %s"
        "</div>",
        broker_html, (unsigned long)s_cfg->mqtt_port,
        state_html,
        (unsigned long)pubs,
        s_cfg->mqtt_topic_prefix[0] ? prefix_esc : "<i>(empty)</i>",
        s_cfg->mqtt_ha_discovery ? "enabled" : "disabled",
        tls_html);
}

// --- Uploads block -----------------------------------------------------------
//
// Per-target succeeded/attempted + last_rc + breaker state, plus FTPS line.
// Targets that aren't enabled in config are omitted (keeps the block tight).
static bool target_enabled(tx_target_id_t id) {
    switch (id) {
        case TX_TARGET_MADAVI:  return s_cfg->send_madavi;
        case TX_TARGET_SENSORC: return s_cfg->send_sensorc;
        case TX_TARGET_RADMON:  return s_cfg->send_radmon;
        case TX_TARGET_OSM:     return s_cfg->send_osm;
        case TX_TARGET_OSM_STAGING: return s_cfg->send_osm_staging;
        case TX_TARGET_AQI:     return s_cfg->send_aqi;
        case TX_TARGET_GMC:        return s_cfg->send_gmc;
        case TX_TARGET_THINGSPEAK: return s_cfg->send_thingspeak;
        case TX_TARGET_THINGSPEAK_PM: return s_cfg->send_thingspeak_pm;
        default:                return false;
    }
}

// Defensive helper: snprintf into a buffer at offset n with bounds check.
// Returns updated n. Stops growing once the buffer is full (further calls
// no-op). Prevents the `sz - n` underflow if a caller miscounted.
static int append_safe(char *out, size_t sz, int n, const char *fmt, ...) {
    if (n < 0 || (size_t)n >= sz) return (int)sz;
    va_list ap;
    va_start(ap, fmt);
    int w = vsnprintf(out + n, sz - n, fmt, ap);
    va_end(ap);
    if (w < 0) return n;
    n += w;
    if ((size_t)n > sz) n = (int)sz;
    return n;
}

// --- CPM history graph data (V2.5.6) -----------------------------------------
// Emits the minute + hour rings as a JS object for the inline SVG graph
// (STATUS_GRAPH). Empty when the tube is disabled — the dust node has no
// radiation history. Values are CPM, only the valid ring entries, oldest..newest.
static void format_history_data(char *out, size_t sz) {
    if (!tube_is_enabled()) { out[0] = 0; return; }
    history_snapshot_t h;
    history_get(&h);
    int n = append_safe(out, sz, 0, "<script>var H={min:[");
    for (uint8_t i = 0; i < h.min_count; i++)
        n = append_safe(out, sz, n, "%s%u", i ? "," : "", (unsigned)h.cpm_min[i]);
    n = append_safe(out, sz, n, "],hour:[");
    for (uint8_t i = 0; i < h.hour_count; i++)
        n = append_safe(out, sz, n, "%s%u", i ? "," : "", (unsigned)h.cpm_hour[i]);
    append_safe(out, sz, n, "]};</script>");
}

static void format_uploads(char *out, size_t sz) {
    int n = append_safe(out, sz, 0,
        "<div class=\"info\"><h3>Uploads</h3>"
        "<table class=u>"
        "<tr><th align=left>Target</th>"
        "<th class=ar>OK / Attempted</th>"
        "<th class=ar>Last rc</th>"
        "<th class=ar>Breaker</th></tr>");

    for (int i = 0; i < TX_TARGET_COUNT; i++) {
        if (!target_enabled(i)) continue;
        tx_target_stats_t s;
        tx_get_stats(i, &s);
        const char *breaker_html =
            (s.breaker_open_cycles == 0) ? "<span class=g>closed</span>" : NULL;
        char breaker_buf[80];
        if (!breaker_html) {
            snprintf(breaker_buf, sizeof(breaker_buf),
                     "<b class=o>open (%d cyc)</b>",
                     s.breaker_open_cycles);
            breaker_html = breaker_buf;
        }
        const char *rc_class =
            (s.attempted == 0)                            ? "d" :
            (s.last_rc >= 200 && s.last_rc < 300)         ? "g" :
            (s.last_rc == -1)                             ? "r" :
                                                            "o";
        char rc_buf[16];
        if (s.attempted == 0) snprintf(rc_buf, sizeof(rc_buf), "—");
        else                  snprintf(rc_buf, sizeof(rc_buf), "%d", s.last_rc);

        n = append_safe(out, sz, n,
            "<tr><td>%s</td>"
            "<td class=ar>%lu / %lu</td>"
            "<td class=\"ar %s\">%s</td>"
            "<td class=ar>%s</td></tr>",
            tx_target_name(i),
            (unsigned long)s.succeeded, (unsigned long)s.attempted,
            rc_class, rc_buf,
            breaker_html);
    }
    n = append_safe(out, sz, n, "</table>");

    // FTPS line — separate from the table because it has its own cadence.
    if (s_cfg->ftp_enabled) {
        log_ftp_stats_t f;
        log_ftp_get_stats(&f);
        char wall[32], ago[24], next_buf[32];
        if (f.have_last) {
            format_wallclock(f.last_at, wall, sizeof(wall));
            format_ago((int64_t)time(NULL), f.last_at, ago, sizeof(ago));
        } else {
            snprintf(wall, sizeof(wall), "never");
            ago[0] = 0;
        }
        // next_due_ms is monotonic uptime ms. Convert to a duration string
        // mirroring format_ago's H/M/S split (V2.3.24 — was "in Nseconds"
        // only, awkward at hourly cadence).
        unsigned long uptime_ms = (unsigned long)(esp_timer_get_time() / 1000LL);
        long remaining_ms = (long)(f.next_due_ms - uptime_ms);
        if (remaining_ms < 0) remaining_ms = 0;
        long rs = remaining_ms / 1000;
        if      (rs < 60)    snprintf(next_buf, sizeof(next_buf), "in %lds", rs);
        else if (rs < 3600)  snprintf(next_buf, sizeof(next_buf), "in %ldm %lds", rs / 60, rs % 60);
        else if (rs < 86400) snprintf(next_buf, sizeof(next_buf), "in %ldh %ldm", rs / 3600, (rs / 60) % 60);
        else                 snprintf(next_buf, sizeof(next_buf), "in %ldd %ldh", rs / 86400, (rs / 3600) % 24);

        const char *result_html;
        if (!f.have_last)         result_html = "—";
        else if (f.last_ok)       result_html = "<span class=g>OK</span>";
        else                      result_html = "<span class=r>FAIL</span>";

        n = append_safe(out, sz, n,
            "<br><b>FTP%s:</b> last %s%s%s &middot; %lu bytes &middot; result %s &middot; next %s",
            s_cfg->ftp_tls ? "S" : "",
            wall,
            f.have_last ? " (" : "",
            f.have_last ? ago  : "",
            (unsigned long)f.last_bytes,
            result_html,
            next_buf);
        if (f.have_last) {
            n = append_safe(out, sz, n, ")");
        }
    }
    append_safe(out, sz, n, "</div>");
}

// --- LoRaWAN block (V2.6.23, T8; BOARD_HELTEC_WIFI_LORA32_V4_R2 only) --------
//
// HAL_HAS_LORAWAN-gated so the ten other boards' /status pages stay byte-
// identical (lorawan_get_status()'s no-op stub would otherwise render a
// "disabled" card everywhere there's no radio to disable). Modeled on the
// adjacent format_mqtt() — a single target's state, not a multi-row table
// like format_uploads(), since there's exactly one LoRaWAN radio per node.
#if HAL_HAS_LORAWAN
static void format_lorawan(char *out, size_t sz) {
    lorawan_status_t st;
    lorawan_get_status(&st);

    const char *state_class =
        (st.state == LORAWAN_ST_JOINED)   ? "g" :
        (st.state == LORAWAN_ST_JOINING)  ? "o" :
        (st.state == LORAWAN_ST_DISABLED) ? "d" : "r";   // no_config / hw_fail

    int n = append_safe(out, sz, 0,
        "<div class=\"info\"><h3>LoRaWAN (TTN)</h3>"
        "<b>State:</b> <span class=\"%s\">%s</span><br>"
        "<b>Region:</b> %s, sub-band %u<br>",
        state_class, lorawan_state_name(st.state),
        lorawan_region_name(st.region), (unsigned)st.subband);

    if (st.state == LORAWAN_ST_JOINED) {
        n = append_safe(out, sz, n, "<b>DevAddr:</b> %08lx<br>", (unsigned long)st.dev_addr);
    }

    n = append_safe(out, sz, n,
        "<b>Join attempts:</b> %lu<br>"
        "<b>Uplinks sent:</b> %lu<br>"
        "<b>Duty-skipped:</b> %lu<br>"
        "<b>Failed:</b> %lu",
        (unsigned long)st.join_attempts,
        (unsigned long)st.uplinks_sent,
        (unsigned long)st.duty_skipped,
        (unsigned long)st.failed);
    if (st.last_error != 0) {
        n = append_safe(out, sz, n, " (last error %d)", (int)st.last_error);
    }

    // format_ago() already renders "never" for a <=0 timestamp — matches
    // last_uplink_at's "0 = never" contract (lorawan.h).
    char ago[24];
    format_ago((int64_t)time(NULL), st.last_uplink_at, ago, sizeof(ago));
    n = append_safe(out, sz, n, "<br><b>Last uplink:</b> %s", ago);

    // last_dl_rssi == 0 means no downlink has ever been seen (lorawan.h).
    if (st.last_dl_rssi != 0) {
        n = append_safe(out, sz, n,
            "<br><b>Last downlink:</b> RSSI %.0f dBm, SNR %.1f dB",
            (double)st.last_dl_rssi, (double)st.last_dl_snr);
    }

    append_safe(out, sz, n, "</div>");
}
#endif

// Favicon — radiation trefoil ☢ (U+2622) on yellow, served as SVG.
static const char s_favicon_svg[] =
    "<svg xmlns='http://www.w3.org/2000/svg' viewBox='0 0 100 100'>"
    "<rect width='100' height='100' rx='14' fill='#FFE000'/>"
    "<text x='50' y='82' font-size='80' text-anchor='middle' fill='#111'>"
    "\xe2\x98\xa2"   // UTF-8 for ☢
    "</text></svg>";

static esp_err_t favicon_get(httpd_req_t *req) {
#if HAL_HAS_HTTPS
    // Not access-logged (one per page load would be noise), but it IS a
    // served request: without this a connection whose only request was the
    // icon would be reported as "closed before any request".
    if (req->handle == s_server) tls_sess_mark_served(httpd_req_to_sockfd(req));
#endif
    httpd_resp_set_type(req, "image/svg+xml");
    httpd_resp_set_hdr(req, "Cache-Control", "max-age=86400");
    return httpd_resp_send(req, s_favicon_svg, HTTPD_RESP_USE_STRLEN);
}

// PM sensor status block. Emits a self-contained <div class="info"> if a PM
// sensor is connected, otherwise an empty string (caller drops it cleanly into
// the page). Reads only from the cache populated by the cycle thread — never
// touches I²C from this HTTP-handler context.
static void format_pm_info(char *out, size_t sz) {
    if (!pm_sensor_present()) {
        out[0] = 0;
        return;
    }
    pm_sensor_status_t st;
    bool have_status = (pm_sensor_get_last_status(&st) == ESP_OK);
    pm_sample_t pm;
    bool have_sample = (pm_sensor_get_last_sample(&pm) == ESP_OK);

    // Pretty status badges with colour. Red for hard faults so they jump out;
    // orange for the soft "fan speed warning"; green for OK. CSS is inline
    // because the parent page only carries minimal styling.
    const char *fan_html =
        !have_status            ? "<span style='color:#888'>unknown</span>" :
        st.fan_fail             ? "<span style='color:#c00;font-weight:bold'>FAULT</span>" :
        st.fan_speed_warn       ? "<span style='color:#c80;font-weight:bold'>SPEED WARN</span>" :
                                  "<span style='color:#080'>OK</span>";
    const char *laser_html =
        !have_status            ? "<span style='color:#888'>unknown</span>" :
        st.laser_fail           ? "<span style='color:#c00;font-weight:bold'>FAULT</span>" :
                                  "<span style='color:#080'>OK</span>";

    int n = append_safe(out, sz, 0,
        "<div class=\"info\"><h3>Particulate matter</h3>"
        "<b>Sensor:</b> %s<br>"
        "<b>Fan:</b> %s<br>"
        "<b>Laser:</b> %s<br>"
        "<b>Status raw:</b> <code>0x%08lx</code><br>",
        pm_sensor_name(), fan_html, laser_html,
        have_status ? (unsigned long)st.raw : 0UL);

    if (have_sample) {
        n = append_safe(out, sz, n,
            "<b>PM1.0 / PM2.5 / PM4.0 / PM10:</b> "
            "%.1f / %.1f / %.1f / %.1f µg/m³<br>"
            "<b>Typical particle size:</b> %.2f µm<br>",
            pm.pm1_0, pm.pm2_5, pm.pm4_0, pm.pm10, pm.typ_size_um);
    } else {
        n = append_safe(out, sz, n,
            "<b>PM readings:</b> awaiting first cycle...<br>");
    }
    append_safe(out, sz, n, "</div>");
}

// Static page chrome — wrapper HTML that doesn't change between requests.
// Sent as string literals via httpd_resp_send_chunk → no per-request copy.
static const char STATUS_HEAD[] =
    "<!doctype html><html><head><meta charset=\"utf-8\">"
    "<link rel=\"icon\" type=\"image/svg+xml\" href=\"/favicon.ico\">"
    "<title>MultiGeiger</title>"
    "<style>body{font-family:sans-serif;max-width:680px;margin:20px auto;padding:0 10px}"
    "h1{color:#333}h3{margin:0 0 6px 0;color:#444}a{color:#0066cc}"
    ".info{background:#f5f5f5;border:1px solid #ddd;padding:10px;border-radius:4px;margin:10px 0}"
    ".u{border-collapse:collapse;font-size:.95em}.ar{text-align:right;padding-left:10px}"
    ".g{color:#080}.r{color:#c00}.o{color:#c80}.d{color:#888}"
    ".fp{font-family:monospace;overflow-wrap:anywhere}"
    "</style></head><body>";
// V2.3.32: split into HEAD + TAIL so status_get can inject the optional
// per-chip Madavi graphs link between them when madavi uploads are enabled.
// Resolved once per page render (no JS): if Madavi is toggled on/off in
// /config, the link only appears/disappears on the next page load.
static const char STATUS_LINKS_HEAD[] =
    "<p><a href=\"/config\">&#9881; Configuration</a> (requires password)</p>"
    "<p><a href=\"/update\">&#11014; Firmware Update (OTA)</a> (requires password)</p>"
    "<p><a href=\"/log\">&#128221; View log buffer</a></p>";
static const char STATUS_LINKS_TAIL[] =
    "</body></html>";

// V2.5.6: CPM-history graph chrome — static SVG + hand-drawn JS (no external
// lib; offline device). Drawing runs in the browser; the device only serves
// this markup + the per-request data object `H` (emitted by format_history_data
// just before this chunk). `Hh` is the SVG height — must NOT shadow the data
// object `H`. Sent verbatim via send_chunk, so `%` is literal.
static const char STATUS_GRAPH[] =
    "<div class='info'><h3>CPM history</h3>"
    "<svg id='hg' viewBox='0 0 320 140' style='width:100%;height:auto;"
    "background:#111;border-radius:4px;font-family:sans-serif'>"
    "<g id='hgrid'></g><g id='hxlab'></g><g id='hylab'></g>"
    "<polyline id='hpl' fill='none' stroke='#4caf50' stroke-width='1.5' points=''/>"
    "<text id='hlbl' x='316' y='11' fill='#888' font-size='9' text-anchor='end'></text>"
    "</svg><br>"
    "<button onclick=\"hdraw('min')\">60 min</button> "
    "<button onclick=\"hdraw('hour')\">24 h</button>"
    "<script>function hdraw(s){"
    "var d=(s=='hour'?H.hour:H.min);"
    "var gr=document.getElementById('hgrid'),yl=document.getElementById('hylab'),"
    "xl=document.getElementById('hxlab'),pl=document.getElementById('hpl'),"
    "lb=document.getElementById('hlbl');"
    "if(!d||!d.length){lb.textContent='no data yet';pl.setAttribute('points','');"
    "gr.innerHTML='';yl.innerHTML='';xl.innerHTML='';return;}"
    "var mx=Math.max.apply(null,d),mn=Math.min.apply(null,d),sp=(mx-mn)||1,n=d.length;"
    "var W=320,Hh=140,L=24,R=6,T=10,B=20,x0=L,x1=W-R,y0=T,y1=Hh-B;"
    "function X(i){return x0+i*(x1-x0)/(n>1?n-1:1);}"
    "function Y(v){return y1-(v-mn)*(y1-y0)/sp;}"
    // horizontal gridlines at every 1 CPM (skipped when the range is huge so we
    // don't emit hundreds of <line>s); emphasise + label round steps.
    "var st=sp>40?10:sp>12?5:1,mok=sp<=45,g='',yt='';"
    "for(var v=Math.ceil(mn);v<=Math.floor(mx);v++){"
    "var bg=(v%st==0);if(!bg&&!mok)continue;var y=Y(v).toFixed(1);"
    "g+='<line x1=\"'+x0+'\" y1=\"'+y+'\" x2=\"'+x1+'\" y2=\"'+y+'\" stroke=\"#fff\" stroke-opacity=\"'+(bg?0.18:0.05)+'\" stroke-width=\"0.5\"/>';"
    "if(bg)yt+='<text x=\"'+(x0-3)+'\" y=\"'+(Y(v)+3).toFixed(1)+'\" fill=\"#888\" font-size=\"8\" text-anchor=\"end\">'+v+'</text>';"
    "}"
    "gr.innerHTML=g;yl.innerHTML=yt;"
    "pl.setAttribute('points',d.map(function(v,i){return X(i).toFixed(1)+','+Y(v).toFixed(1);}).join(' '));"
    // x-axis reading times — newest point = now (viewer's clock), evenly spaced.
    "var ms=(s=='hour'?3600000:60000),nw=Date.now(),xt='',tk=Math.min(5,n);"
    "for(var k=0;k<tk;k++){"
    "var i=Math.round(k*(n-1)/(tk>1?tk-1:1)),t=new Date(nw-(n-1-i)*ms);"
    "var hh=('0'+t.getHours()).slice(-2)+':'+('0'+t.getMinutes()).slice(-2),xx=X(i).toFixed(1);"
    "xt+='<line x1=\"'+xx+'\" y1=\"'+y0+'\" x2=\"'+xx+'\" y2=\"'+y1+'\" stroke=\"#fff\" stroke-opacity=\"0.05\" stroke-width=\"0.5\"/>';"
    "xt+='<text x=\"'+xx+'\" y=\"'+(Hh-7)+'\" fill=\"#888\" font-size=\"8\" text-anchor=\"middle\">'+hh+'</text>';"
    "}"
    "xl.innerHTML=xt;"
    "lb.textContent=(s=='hour'?'last '+n+' h':'last '+n+' min');}"
    "hdraw('min');</script></div>";

// Streaming-friendly send: skip if format function emitted nothing (the
// "block hidden" case for radiation/env/noise/PM). Returns false on
// transport error — caller bails immediately.
static bool send_block(httpd_req_t *req, const char *buf) {
    size_t len = strlen(buf);
    if (len == 0) return true;
    return httpd_resp_send_chunk(req, buf, len) == ESP_OK;
}

static esp_err_t status_get(httpd_req_t *req) {
    log_access(req, "GET /");
    // Single shared scratch buffer reused across all blocks. Sized for the
    // worst-case block (uploads with 5 enabled targets ≈ 1.4 KB). Stream each
    // chunk via httpd chunked transfer-encoding — same pattern V2.3.17 used
    // for /log to avoid heap-pressure transient peaks.
    //
    // V2.4.22: moved from stack to BSS. 1.6 KB on the httpd task's 8 KB
    // stack stacks with config_get's escape buffers and format_system's
    // cd_summary/cd_line on adjacent /status renders. Safe because
    // esp_http_server uses a single thread (httpd_thread runs all URI
    // handlers serially), so this handler is never re-entered; the entire
    // function fills buf then sends each block before next overwrite.
    static char buf[1600];
    int64_t       now_us    = esp_timer_get_time();
    // uptime_ms stays crystal-based (esp_timer) because format_cycle compares
    // it against last_cycle_ms which is also esp_timer — mixing time bases
    // there would corrupt the "Next cycle in Xs" display.
    unsigned long uptime_ms = (unsigned long)(now_us / 1000LL);
    // Capture wall clock once so "clock now" in format_system and "Started +
    // Uptime" below are always rooted in the same timestamp.
    time_t        now_wall   = time(NULL);
    time_t        boot_ep    = ntp_boot_epoch();
    time_t        uptime_t   = boot_ep
        ? now_wall - boot_ep
        : (time_t)(now_us / 1000000LL);
    unsigned long uptime_s   = uptime_t > 0 ? (unsigned long)uptime_t : 0UL;

    httpd_resp_set_type(req, "text/html; charset=utf-8");

    if (httpd_resp_send_chunk(req, STATUS_HEAD, sizeof(STATUS_HEAD) - 1) != ESP_OK) goto fail;

    // Title — small, dynamic, fits trivially.
    int n = snprintf(buf, sizeof(buf), "<h1>&#9762; MultiGeiger %s</h1>", VERSION_STR);
    if (httpd_resp_send_chunk(req, buf, n) != ESP_OK) goto fail;

    format_device     (buf, sizeof(buf)); if (!send_block(req, buf)) goto fail;
    format_net_info   (buf, sizeof(buf)); if (!send_block(req, buf)) goto fail;
    format_system     (buf, sizeof(buf), uptime_s, now_wall);  if (!send_block(req, buf)) goto fail;
    format_cycle      (buf, sizeof(buf), uptime_ms); if (!send_block(req, buf)) goto fail;
    format_radiation  (buf, sizeof(buf)); if (!send_block(req, buf)) goto fail;
    // V2.5.6: CPM-history graph — radiation nodes only. Data object first, then
    // the static SVG+JS chrome that draws it.
    if (tube_is_enabled()) {
        format_history_data(buf, sizeof(buf)); if (!send_block(req, buf)) goto fail;
        if (httpd_resp_send_chunk(req, STATUS_GRAPH, sizeof(STATUS_GRAPH) - 1) != ESP_OK) goto fail;
    }
    format_environment(buf, sizeof(buf)); if (!send_block(req, buf)) goto fail;
    format_als        (buf, sizeof(buf)); if (!send_block(req, buf)) goto fail;
    format_battery    (buf, sizeof(buf)); if (!send_block(req, buf)) goto fail;
    format_gnss       (buf, sizeof(buf)); if (!send_block(req, buf)) goto fail;
#if HAL_HAS_SD_CARD
    format_sd_logger  (buf, sizeof(buf)); if (!send_block(req, buf)) goto fail;
#endif
    format_noise      (buf, sizeof(buf)); if (!send_block(req, buf)) goto fail;
    format_sgp41      (buf, sizeof(buf)); if (!send_block(req, buf)) goto fail;
    format_pm_info    (buf, sizeof(buf)); if (!send_block(req, buf)) goto fail;
    format_uploads    (buf, sizeof(buf)); if (!send_block(req, buf)) goto fail;
#if HAL_HAS_LORAWAN
    format_lorawan    (buf, sizeof(buf)); if (!send_block(req, buf)) goto fail;
#endif
    format_mqtt       (buf, sizeof(buf)); if (!send_block(req, buf)) goto fail;

    if (httpd_resp_send_chunk(req, STATUS_LINKS_HEAD, sizeof(STATUS_LINKS_HEAD) - 1) != ESP_OK) goto fail;

    // V2.3.32: optional per-chip Madavi graph link. Only emitted if the
    // user has Madavi uploads enabled — there's no point linking to a graph
    // page that has no data behind it. The dashboard ID + path are baked in
    // from the user's confirmed working URL on 2026-05-16; if Madavi ever
    // restructures the Grafana URL space we'll need to refresh it here.
    if (s_cfg && s_cfg->send_madavi && s_chip_id && s_chip_id[0]) {
        n = snprintf(buf, sizeof(buf),
            "<p><a href=\"https://api-rrd.madavi.de:3000/grafana/d/q87EBfWGk/"
            "temperature-humidity-pressure?var-chipID=%s\" target=\"_blank\" "
            "rel=\"noopener\">&#128202; Madavi graphs for %s</a></p>",
            s_chip_id, s_chip_id);
        if (httpd_resp_send_chunk(req, buf, n) != ESP_OK) goto fail;
    }

    if (httpd_resp_send_chunk(req, STATUS_LINKS_TAIL, sizeof(STATUS_LINKS_TAIL) - 1) != ESP_OK) goto fail;
    httpd_resp_send_chunk(req, NULL, 0);   // end-of-stream sentinel
    return ESP_OK;
fail:
    // Best-effort terminate the chunked stream so the socket isn't half-open.
    httpd_resp_send_chunk(req, NULL, 0);
    return ESP_FAIL;
}

// --- GET /config (auth'd form) -----------------------------------------------

// Bumped from 6144 in V2.3.3 — adding the openSenseMap + aqi.eco rows pushed
// the worst-case formatted length past the old ceiling. V2.3.33: bumped 8192
// → 16384 after silent snprintf truncation surfaced as missing page tail on
// devices with longer field values (longer SSIDs/FTP paths/tokens consumed
// the remaining budget; cut point varied per board because field lengths
// varied). 16 KB gives ~8 KB headroom; truncation is now also logged at
// ERROR level (see config_get) so any future near-miss is loud, not silent.
//
// V2.4.6: per-board buffer size — moved to hal.h. Heltec V2 runs 24 KB
// (V2.5.29, tight internal-DRAM budget; the "16 KB" this comment used to
// claim is two bumps stale), every other board 32 KB — room for the MQTT
// TLS PEM textarea + future config sections without stressing heap on
// PSRAM-backed boards.
#define CFG_FORM_BUF_SIZE HAL_CFG_FORM_BUF_SIZE

static esp_err_t config_get(httpd_req_t *req) {
    log_access(req, "GET /config");
    if (!check_auth(req)) return ESP_OK;

    char *body = malloc(CFG_FORM_BUF_SIZE);
    if (!body) {
        httpd_resp_send_err(req, HTTPD_500_INTERNAL_SERVER_ERROR, "oom");
        return ESP_OK;
    }

    // Escape every string field for safe use in value="..." attributes.
    //
    // V2.6.24: the whole e_* workspace is ONE heap-transient struct, each
    // field sized ESC_WORST(its source's CFG_*_MAX) — see the ESC_WORST
    // comment at the top of this file for why the previous ~3-4x static
    // sizes were wrong (truncate-then-persist-back on Save). Heap rather
    // than the V2.4.22 BSS statics because at full 6x sizing the workspace
    // is ~9 KB: as BSS that would tax every board permanently (the Heltec
    // V2's internal-DRAM budget is the tightest), while as a malloc it
    // exists only while a /config GET is in flight — a path that already
    // heap-allocates CFG_FORM_BUF_SIZE (24-32 KB) + the PEM buffer, with a
    // graceful 500-on-OOM. This also RETURNS the old ~4.4 KB of BSS to the
    // heap. Stack was never an option (V2.4.22: 8 KB httpd stack budget).
    // html_esc() fully overwrites each field before the big snprintf reads
    // it, so plain malloc (no calloc) is sufficient.
    typedef struct {
        char ssid       [ESC_WORST(CFG_WIFI_SSID_MAX)];
        char pw         [ESC_WORST(CFG_WIFI_PSK_MAX)];
        char chip       [96];   // chip id: digits/dashes only, never expands
        char ru         [ESC_WORST(CFG_USER_NAME_MAX)];
        char rp         [ESC_WORST(CFG_PASSWORD_MAX)];
        char ntp1       [ESC_WORST(CFG_NTP_HOST_MAX)];
        char ntp2       [ESC_WORST(CFG_NTP_HOST_MAX)];
        char ntp3       [ESC_WORST(CFG_NTP_HOST_MAX)];
        char ap         [ESC_WORST(CFG_AP_PW_MAX)];
        char tz         [ESC_WORST(CFG_TZ_POSIX_MAX)];
        char apn        [ESC_WORST(CFG_AP_NAME_MAX)];
        char host       [ESC_WORST(CFG_HOSTNAME_MAX)];
        char fhost      [ESC_WORST(CFG_FTP_HOST_MAX)];
        char fuser      [ESC_WORST(CFG_USER_NAME_MAX)];
        char fpw        [ESC_WORST(CFG_PASSWORD_MAX)];
        char fpath      [ESC_WORST(CFG_FTP_PATH_MAX)];
        char osm        [ESC_WORST(CFG_OSM_BOX_MAX)];
        char osm_tok    [ESC_WORST(CFG_TOKEN_MAX)];
        char aqi        [ESC_WORST(CFG_TOKEN_MAX)];
        char osm_st     [ESC_WORST(CFG_OSM_BOX_MAX)];   // V2.5.26: OSM staging
        char osm_st_tok [ESC_WORST(CFG_TOKEN_MAX)];
        // V2.5.1: GMCMap + ThingSpeak. Numeric/hex by validation, but escaped
        // for the same defence-in-depth reason as the LoRa fields below.
        char gmc_aid    [ESC_WORST(CFG_USER_NAME_MAX)];
        char gmc_gid    [ESC_WORST(CFG_USER_NAME_MAX)];
        char ts_key     [ESC_WORST(CFG_TOKEN_MAX)];
        char ts_pm_key  [ESC_WORST(CFG_TOKEN_MAX)];     // V2.5.4: ThingSpeak PM
        char mhost      [ESC_WORST(CFG_MQTT_HOST_MAX)];
        char muser      [ESC_WORST(CFG_USER_NAME_MAX)];
        char mpw        [ESC_WORST(CFG_PASSWORD_MAX)];
        char mpfx       [ESC_WORST(CFG_MQTT_PFX_MAX)];
        char slh        [ESC_WORST(CFG_SYSLOG_HOST_MAX)];   // V2.4.15: syslog
#if HAL_HAS_LORAWAN
        // V2.6.23 (T8): DevEUI/JoinEUI/AppKey are plain hex strings — no HTML
        // metacharacters possible in a value that later passes lw_hex_decode —
        // but escaped anyway: defence-in-depth against a stored value that
        // predates/bypasses POST validation (hand-crafted request, NVS carried
        // over from a future firmware).
        char lora_deveui [ESC_WORST(CFG_LORA_EUI_MAX)];
        char lora_joineui[ESC_WORST(CFG_LORA_EUI_MAX)];
        char lora_appkey [ESC_WORST(CFG_LORA_KEY_MAX)];
#endif
    } esc_bufs_t;
    esc_bufs_t *e = malloc(sizeof(*e));
    if (!e) {
        free(body);
        httpd_resp_send_err(req, HTTPD_500_INTERNAL_SERVER_ERROR, "oom");
        return ESP_OK;
    }
    // V2.4.6: MQTT TLS PEM cert, its own allocation (folding it into the
    // struct above would make that a single ~23 KB contiguous ask — two
    // smaller allocs are kinder to a fragmented heap). V2.6.24: sized to the
    // honest 6x worst case (the old 8192 comment claimed it "covers even
    // pathological inputs", which 6 x 2400 = 14400 disproves); real PEM is
    // mostly base64 so the extra 6 KB transient is never touched in practice.
    char *e_mca = malloc(ESC_WORST(CFG_MQTT_CA_CERT_MAX));
    if (!e_mca) {
        free(e);
        free(body);
        httpd_resp_send_err(req, HTTPD_500_INTERNAL_SERVER_ERROR, "oom");
        return ESP_OK;
    }
    html_esc(s_cfg->wifi_ssid,     e->ssid, sizeof(e->ssid));
    html_esc(s_cfg->wifi_password, e->pw,   sizeof(e->pw));
    html_esc(s_chip_id,            e->chip, sizeof(e->chip));  // read-only display
    html_esc(s_cfg->radmon_user,   e->ru,   sizeof(e->ru));
    html_esc(s_cfg->radmon_password, e->rp, sizeof(e->rp));
    html_esc(s_cfg->ntp_server,    e->ntp1, sizeof(e->ntp1));
    html_esc(s_cfg->ntp_server2,   e->ntp2, sizeof(e->ntp2));
    html_esc(s_cfg->ntp_server3,   e->ntp3, sizeof(e->ntp3));
    html_esc(s_cfg->tz_posix,      e->tz,   sizeof(e->tz));
    html_esc(s_cfg->ap_password,   e->ap,   sizeof(e->ap));
    html_esc(s_cfg->ap_name,       e->apn,  sizeof(e->apn));
    html_esc(s_cfg->wifi_hostname, e->host, sizeof(e->host));
    html_esc(s_cfg->ftp_host,      e->fhost, sizeof(e->fhost));
    html_esc(s_cfg->ftp_user,      e->fuser, sizeof(e->fuser));
    html_esc(s_cfg->ftp_password,  e->fpw,   sizeof(e->fpw));
    html_esc(s_cfg->ftp_path,      e->fpath, sizeof(e->fpath));
    html_esc(s_cfg->osm_box_id,       e->osm,     sizeof(e->osm));
    html_esc(s_cfg->osm_access_token, e->osm_tok, sizeof(e->osm_tok));
    html_esc(s_cfg->osm_staging_box_id, e->osm_st,     sizeof(e->osm_st));
    html_esc(s_cfg->osm_staging_token,  e->osm_st_tok, sizeof(e->osm_st_tok));
    html_esc(s_cfg->aqi_token,        e->aqi,     sizeof(e->aqi));
    html_esc(s_cfg->gmc_account_id,     e->gmc_aid, sizeof(e->gmc_aid));
    html_esc(s_cfg->gmc_geiger_id,      e->gmc_gid, sizeof(e->gmc_gid));
    html_esc(s_cfg->thingspeak_api_key, e->ts_key,  sizeof(e->ts_key));
    html_esc(s_cfg->thingspeak_pm_api_key, e->ts_pm_key, sizeof(e->ts_pm_key));
    html_esc(s_cfg->mqtt_broker,       e->mhost, sizeof(e->mhost));
    html_esc(s_cfg->mqtt_user,         e->muser, sizeof(e->muser));
    html_esc(s_cfg->mqtt_password,     e->mpw,   sizeof(e->mpw));
    html_esc(s_cfg->mqtt_topic_prefix, e->mpfx,  sizeof(e->mpfx));
    html_esc(s_cfg->mqtt_tls_ca,       e_mca,   ESC_WORST(CFG_MQTT_CA_CERT_MAX));
    html_esc(s_cfg->syslog_host,       e->slh,   sizeof(e->slh));
#if HAL_HAS_LORAWAN
    html_esc(s_cfg->lorawan_deveui,    e->lora_deveui,  sizeof(e->lora_deveui));
    html_esc(s_cfg->lorawan_joineui,   e->lora_joineui, sizeof(e->lora_joineui));
    html_esc(s_cfg->lorawan_appkey,    e->lora_appkey,  sizeof(e->lora_appkey));
#endif

    // V2.3.30: build the display-brightness <option> list dynamically — OFF
    // (0 %) followed by 10 % through 100 % in 10 % steps. Builder keeps the
    // main snprintf args list sane (one extra %s instead of eleven "selected"
    // vs "" args). V2.3.32: added OFF entry — turns the SerLCD backlight
    // fully dark (panel pixels still drawn but invisible) and powers the
    // OLED panel down via 0xAE (zero-current state). See display_set_contrast.
    // V2.4.22: br_opts also static — same justification as the e_* block above.
    static char br_opts[512];
    int br_n = 0;
    br_n += snprintf(br_opts + br_n, sizeof(br_opts) - br_n,
                     "<option value=\"0\"%s>OFF</option>",
                     (s_cfg->oled_brightness_pct == 0) ? " selected" : "");
    for (int v = 10; v <= 100; v += 10) {
        br_n += snprintf(br_opts + br_n, sizeof(br_opts) - br_n,
                         "<option value=\"%d\"%s>%d%%</option>",
                         v,
                         (s_cfg->oled_brightness_pct == v) ? " selected" : "",
                         v);
    }

    // V2.6.1: tube-type dropdown options built from the shared tube_types table
    // (single source of truth) instead of hardcoded <option> lines + per-option
    // selected-marker args. append_safe keeps the accumulation truncation-safe.
    // V2.6.4: static — same justification as e_* + br_opts (V2.4.22).
    static char tube_opts[384];
    int tube_n = 0;
    for (uint32_t t = 0; t < TUBE_TYPE_COUNT; t++) {
        tube_n = append_safe(tube_opts, sizeof(tube_opts), tube_n,
                             "<option value=\"%lu\"%s>%s%s</option>",
                             (unsigned long)t,
                             (s_cfg->tube_type == t) ? " selected" : "",
                             tube_type_name(t), tube_type_menu_suffix(t));
    }

#if HAL_HAS_LORAWAN
    // V2.6.23 (T8): LoRaWAN region <option> list, table-driven like tube_opts/
    // br_opts above — one %s instead of 8 per-option "selected" args. Names
    // match lorawan.cpp's REGION_NAMES (lorawan_region_name()) 1:1; kept as a
    // literal local table here (rather than calling lorawan_region_name() in
    // a loop) so this stays plain-string, no round-trip through that API.
    static char lora_region_opts[320];
    {
        static const char *const k_lora_region_names[] = {
            "EU868", "US915", "AU915", "AS923", "IN865", "KR920", "EU433", "CN470"
        };
        int lora_rn = 0;
        for (uint8_t r = 0; r < 8; r++) {
            lora_rn = append_safe(lora_region_opts, sizeof(lora_region_opts), lora_rn,
                                 "<option value=\"%u\"%s>%s</option>",
                                 (unsigned)r,
                                 (s_cfg->lorawan_region == r) ? " selected" : "",
                                 k_lora_region_names[r]);
        }
    }
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
