MMBytes/MultiGeiger-V2/main/bme280.c

#include "bme280.h"

#include <string.h>
#include "driver/i2c_master.h"
#include "esp_log.h"
#include "esp_rom_sys.h"     // V2.8.5: esp_rom_delay_us (sub-tick waits)
#include "freertos/FreeRTOS.h"
#include "freertos/task.h"
#include "i2c_bus.h"
#include "telemetry.h"

static const char *TAG = "bme280";

#define I2C_FREQ_HZ    100000

#define BME_ADDR_A     0x76
#define BME_ADDR_B     0x77

// --- Registers ---------------------------------------------------------------
#define REG_CAL_TP     0x88   // 26 bytes: T1..T3, P1..P9, then pad to 0xA1
#define REG_CAL_H1     0xA1
#define REG_ID         0xD0   // should read 0x60
#define REG_RESET      0xE0   // write 0xB6 for soft reset
#define REG_CAL_H2     0xE1   // 7 bytes: H2..H6 (H4/H5 pack across E4/E5/E6)
#define REG_CTRL_HUM   0xF2
#define REG_STATUS     0xF3
#define REG_CTRL_MEAS  0xF4
#define REG_CONFIG     0xF5
#define REG_DATA       0xF7   // 8 bytes: P(3) T(3) H(2)

#define CHIP_ID_BME280 0x60

// --- Oversampling / filter settings -----------------------------------------
// Forced-mode profile, matching BMP390 / BME688 driver pattern in this project.
// Mode bits in ctrl_meas are set per-read by bme280_read() (sleep at init,
// forced for each conversion, then auto-return to sleep).
//   ctrl_hum:        osrs_h = x1 (001)
//   ctrl_meas BASE:  osrs_t = x2 (010) | osrs_p = x16 (101) | mode bits = 00 sleep
//   ctrl_meas READ:  CTRL_MEAS_BASE | 0x01 (forced — datasheet 5.4.5)
//   config:          t_sb irrelevant in forced mode | filter = OFF (000) | spi3w_en = 0
// Oversampling matches Bosch's "Indoor navigation" preset (datasheet table 9):
//   - P x16: best per-read pressure resolution (~0.16 Pa, ~1.4 cm altitude).
//   - T x2:  intentionally low to minimise self-heating bias on T (which would
//            propagate to H via the calibration formula). Bosch specifically
//            recommends NOT going higher than T x2 for accuracy work.
//   - H x1:  going higher only takes humidity noise from 0.008 → 0.002 %RH,
//            well below the ±3 %RH chip accuracy spec — wasted conversion time.
// IIR filter is off: at our 150 s read interval the filter time-constant becomes
// pure latency rather than useful smoothing (oversampling already does multi-
// sample averaging within each forced conversion).
#define CTRL_HUM_VAL    0x01
#define CTRL_MEAS_BASE  ((0x02 << 5) | (0x05 << 2))   // mode = sleep; OR 0x01 to force
#define CONFIG_VAL      0x00                          // filter off, spi3w off

// --- State -------------------------------------------------------------------
static i2c_master_bus_handle_t  s_bus   = NULL;
static i2c_master_dev_handle_t  s_dev   = NULL;
static bool                     s_ready = false;

// V2.6.19: last-read cache consumed by the telemetry read callbacks below.
// Written ONLY by bme280_read(); read ONLY by sd_logger's row build on the
// same task — no locking needed. Invalidated on read failure so the CSV
// emits an empty cell, never stale data.
static bool  s_tm_valid;
static float s_tm_t_c;
static float s_tm_h_pct;
static float s_tm_p_pa;

static bool tm_read_t(char *cell, size_t cap, void *arg) {
    (void)arg;
    if (!s_tm_valid) return false;
    snprintf(cell, cap, "%.2f", (double)s_tm_t_c);
    return true;
}

static bool tm_read_h(char *cell, size_t cap, void *arg) {
    (void)arg;
    if (!s_tm_valid) return false;
    snprintf(cell, cap, "%.2f", (double)s_tm_h_pct);
    return true;
}

static bool tm_read_p(char *cell, size_t cap, void *arg) {
    (void)arg;
    if (!s_tm_valid) return false;
    snprintf(cell, cap, "%.2f", (double)s_tm_p_pa / 100.0);
    return true;
}

// Raw Bosch calibration. Names match the datasheet so the compensation
// formulas below read like the reference implementation.
static uint16_t dig_T1;
static int16_t  dig_T2, dig_T3;
static uint16_t dig_P1;
static int16_t  dig_P2, dig_P3, dig_P4, dig_P5, dig_P6, dig_P7, dig_P8, dig_P9;
static uint8_t  dig_H1, dig_H3;
static int16_t  dig_H2, dig_H4, dig_H5;
static int8_t   dig_H6;

// --- Init --------------------------------------------------------------------

static esp_err_t attach_dev(uint8_t addr) {
    i2c_dev_teardown(&s_dev);
    return i2c_add_device(s_bus, addr, I2C_FREQ_HZ, &s_dev);
}

static esp_err_t probe_and_attach(uint8_t *found_addr, bool skip_addr_77) {
    const uint8_t candidates[2] = { BME_ADDR_A, BME_ADDR_B };
    for (int i = 0; i < 2; i++) {
        if (skip_addr_77 && candidates[i] == BME_ADDR_B) continue;
        if (i2c_master_probe(s_bus, candidates[i], 100) == ESP_OK) {
            esp_err_t err = attach_dev(candidates[i]);
            if (err != ESP_OK) return err;
            uint8_t id = 0;
            if (i2c_dev_read_regs(s_dev, REG_ID, &id, 1) == ESP_OK && id == CHIP_ID_BME280) {
                *found_addr = candidates[i];
                return ESP_OK;
            }
        }
    }
    return ESP_ERR_NOT_FOUND;
}

static esp_err_t read_calibration(void) {
    // T1..T3, P1..P9 live at 0x88..0x9F (24 bytes, little-endian pairs)
    uint8_t tp[24];
    esp_err_t err = i2c_dev_read_regs(s_dev, REG_CAL_TP, tp, sizeof(tp));
    if (err != ESP_OK) return err;

    dig_T1 = (uint16_t)(tp[0]  | (tp[1]  << 8));
    dig_T2 = (int16_t) (tp[2]  | (tp[3]  << 8));
    dig_T3 = (int16_t) (tp[4]  | (tp[5]  << 8));
    dig_P1 = (uint16_t)(tp[6]  | (tp[7]  << 8));
    dig_P2 = (int16_t) (tp[8]  | (tp[9]  << 8));
    dig_P3 = (int16_t) (tp[10] | (tp[11] << 8));
    dig_P4 = (int16_t) (tp[12] | (tp[13] << 8));
    dig_P5 = (int16_t) (tp[14] | (tp[15] << 8));
    dig_P6 = (int16_t) (tp[16] | (tp[17] << 8));
    dig_P7 = (int16_t) (tp[18] | (tp[19] << 8));
    dig_P8 = (int16_t) (tp[20] | (tp[21] << 8));
    dig_P9 = (int16_t) (tp[22] | (tp[23] << 8));

    err = i2c_dev_read_regs(s_dev, REG_CAL_H1, &dig_H1, 1);
    if (err != ESP_OK) return err;

    uint8_t h[7];
    err = i2c_dev_read_regs(s_dev, REG_CAL_H2, h, sizeof(h));
    if (err != ESP_OK) return err;
    dig_H2 = (int16_t)(h[0] | (h[1] << 8));
    dig_H3 = h[2];
    // dig_H4: 12-bit signed, H4[11:4] in 0xE4, H4[3:0] in low nibble of 0xE5
    dig_H4 = (int16_t)(((int16_t)(int8_t)h[3] << 4) | (h[4] & 0x0F));
    // dig_H5: 12-bit signed, H5[3:0] in high nibble of 0xE5, H5[11:4] in 0xE6
    dig_H5 = (int16_t)(((int16_t)(int8_t)h[5] << 4) | (h[4] >> 4));
    dig_H6 = (int8_t)h[6];
    return ESP_OK;
}

esp_err_t bme280_init(i2c_master_bus_handle_t bus, bool skip_addr_77) {
    if (s_ready) return ESP_OK;

    // Bus is owned by env_sensor — just record the handle for our helpers.
    s_bus = bus;

    uint8_t addr = 0;
    esp_err_t err = probe_and_attach(&addr, skip_addr_77);
    if (err != ESP_OK) {
        ESP_LOGW(TAG, "BME280 not found on I2C (tried %s)",
                 skip_addr_77 ? "0x76 only" : "0x76 and 0x77");
        return err;
    }
    ESP_LOGI(TAG, "BME280 found at 0x%02X (chip ID 0x60 verified)", addr);

    // Soft reset, give the chip its 2 ms settling time, then poll the
    // calibration-copying bit until the NVM is ready (datasheet 5.4.1).
    // V2.8.5: precise busy-waits, as in the V2.3.31 sweep of the other
    // drivers. At CONFIG_FREERTOS_HZ=100, pdMS_TO_TICKS(5) and (2) are 0
    // ticks — vTaskDelay(0) is a bare yield — so the reset settle and the
    // poll back-off did not wait at all, and the calibration read could land
    // mid NVM copy. 5 ms + up to 20 x 2 ms runs once, at boot.
    err = i2c_dev_write_reg(s_dev, REG_RESET, 0xB6);
    if (err != ESP_OK) return err;
    esp_rom_delay_us(5000);
    for (int i = 0; i < 20; i++) {
        uint8_t status = 0;
        if (i2c_dev_read_regs(s_dev, REG_STATUS, &status, 1) == ESP_OK && !(status & 0x01)) break;
        esp_rom_delay_us(2000);
    }

    err = read_calibration();
    if (err != ESP_OK) {
        ESP_LOGE(TAG, "calibration read failed: %s", esp_err_to_name(err));
        return err;
    }

    // ctrl_hum must be written BEFORE ctrl_meas (datasheet 5.4.3).
    // Mode bits left at 00 (sleep) here — bme280_read() flips them to forced per call.
    if ((err = i2c_dev_write_reg(s_dev, REG_CTRL_HUM,  CTRL_HUM_VAL))   != ESP_OK) return err;
    if ((err = i2c_dev_write_reg(s_dev, REG_CTRL_MEAS, CTRL_MEAS_BASE)) != ESP_OK) return err;
    if ((err = i2c_dev_write_reg(s_dev, REG_CONFIG,    CONFIG_VAL))     != ESP_OK) return err;

    s_ready = true;
    ESP_LOGI(TAG, "BME280 ready (osrs T=x2 P=x16 H=x1, filter off, forced mode)");

    // V2.6.19: register our CSV columns once. Guards against a second,
    // idempotent init call (env_sensor's dual-bus probe) double-registering.
    static bool s_tm_registered = false;
    if (!s_tm_registered) {
        s_tm_registered = true;
        telemetry_register("BME280 Temperature [C]", tm_read_t, NULL);
        telemetry_register("BME280 Humidity [%]",    tm_read_h, NULL);
        telemetry_register("BME280 Pressure [hPa]",  tm_read_p, NULL);
    }
    return ESP_OK;
}

bool bme280_present(void) {
    return s_ready;
}

i2c_master_bus_handle_t bme280_get_i2c_bus(void) {
    return s_bus;
}

// --- Compensation (Bosch reference, datasheet 8.2) --------------------------

static int32_t  compensate_T_int32(int32_t adc_T, int32_t *t_fine_out) {
    int32_t var1 = ((((adc_T >> 3) - ((int32_t)dig_T1 << 1))) * ((int32_t)dig_T2)) >> 11;
    int32_t var2 = (((((adc_T >> 4) - ((int32_t)dig_T1)) *
                      ((adc_T >> 4) - ((int32_t)dig_T1))) >> 12) *
                    ((int32_t)dig_T3)) >> 14;
    int32_t t_fine = var1 + var2;
    if (t_fine_out) *t_fine_out = t_fine;
    return (t_fine * 5 + 128) >> 8;  // °C * 100
}

static uint32_t compensate_P_int64(int32_t adc_P, int32_t t_fine) {
    int64_t var1 = (int64_t)t_fine - 128000;
    int64_t var2 = var1 * var1 * (int64_t)dig_P6;
    var2 += ((var1 * (int64_t)dig_P5) << 17);
    var2 += ((int64_t)dig_P4) << 35;
    var1  = ((var1 * var1 * (int64_t)dig_P3) >> 8) + ((var1 * (int64_t)dig_P2) << 12);
    var1  = (((((int64_t)1) << 47) + var1)) * ((int64_t)dig_P1) >> 33;
    if (var1 == 0) return 0;
    int64_t p = 1048576 - adc_P;
    p = (((p << 31) - var2) * 3125) / var1;
    var1 = (((int64_t)dig_P9) * (p >> 13) * (p >> 13)) >> 25;
    var2 = (((int64_t)dig_P8) * p) >> 19;
    p = ((p + var1 + var2) >> 8) + (((int64_t)dig_P7) << 4);
    return (uint32_t)p;  // Q24.8 Pa
}

static uint32_t compensate_H_int32(int32_t adc_H, int32_t t_fine) {
    int32_t v = t_fine - 76800;
    v = ((((adc_H << 14) - ((int32_t)dig_H4 << 20) - ((int32_t)dig_H5 * v)) +
          16384) >> 15) *
        (((((((v * (int32_t)dig_H6) >> 10) *
             (((v * (int32_t)dig_H3) >> 11) + 32768)) >> 10) + 2097152) *
           (int32_t)dig_H2 + 8192) >> 14);
    v = v - (((((v >> 15) * (v >> 15)) >> 7) * (int32_t)dig_H1) >> 4);
    if (v < 0) v = 0;
    if (v > 419430400) v = 419430400;
    return (uint32_t)(v >> 12);  // %RH * 1024
}

// --- Read --------------------------------------------------------------------

esp_err_t bme280_read(float *t_out, float *h_out, float *p_out) {
    if (!s_ready) {
        s_tm_valid = false;
        return ESP_FAIL;
    }

    // Trigger one forced-mode conversion. Writing the mode bits to ctrl_meas
    // wakes the chip, runs T/P/H acquisition with the configured oversampling,
    // then returns to sleep automatically.
    esp_err_t err = i2c_dev_write_reg(s_dev, REG_CTRL_MEAS, CTRL_MEAS_BASE | 0x01);
    if (err != ESP_OK) {
        s_tm_valid = false;
        return err;
    }

    // T x2 + P x16 + H x1 worst-case measurement time per datasheet 9.1:
    //   t_meas = 1.25 + 2.3*2 + (2.3*16 + 0.575) + (2.3*1 + 0.575) ≈ 46.1 ms
    // V2.3.31: bumped 55 → 70 ms. At CONFIG_FREERTOS_HZ=100 (10 ms tick),
    // pdMS_TO_TICKS(55) = 5 ticks → 40..50 ms actual sleep, sometimes BELOW
    // the chip's 46.1 ms requirement → stale-register read with no error.
    // pdMS_TO_TICKS(70) = 7 ticks → 60..70 ms guaranteed minimum 60 ms.
    vTaskDelay(pdMS_TO_TICKS(70));

    uint8_t d[8];
    err = i2c_dev_read_regs(s_dev, REG_DATA, d, sizeof(d));
    if (err != ESP_OK) {
        s_tm_valid = false;
        return err;
    }

    int32_t adc_P = (int32_t)(((uint32_t)d[0] << 12) | ((uint32_t)d[1] << 4) | (d[2] >> 4));
    int32_t adc_T = (int32_t)(((uint32_t)d[3] << 12) | ((uint32_t)d[4] << 4) | (d[5] >> 4));
    int32_t adc_H = (int32_t)(((uint32_t)d[6] << 8)  |  (uint32_t)d[7]);

    // Sensor reports 0x80000 on T/P and 0x8000 on H when a channel is
    // disabled or still settling. We configured all three, so treat these
    // as a transient I/O hiccup and surface an error rather than compute.
    if (adc_T == 0x80000 || adc_P == 0x80000 || adc_H == 0x8000) {
        s_tm_valid = false;
        return ESP_FAIL;
    }

    int32_t t_fine;
    int32_t  T  = compensate_T_int32(adc_T, &t_fine);
    uint32_t P  = compensate_P_int64(adc_P, t_fine);
    uint32_t H  = compensate_H_int32(adc_H, t_fine);

    float t_c   = T / 100.0f;
    float p_pa  = P / 256.0f;
    float h_pct = H / 1024.0f;

    if (t_out) *t_out = t_c;
    if (p_out) *p_out = p_pa;
    if (h_out) *h_out = h_pct;

    // V2.6.19: cache from the LOCAL computed values, not the (possibly NULL)
    // out-pointers — the telemetry callbacks above read this cache.
    s_tm_t_c   = t_c;
    s_tm_h_pct = h_pct;
    s_tm_p_pa  = p_pa;
    s_tm_valid = true;
    return ESP_OK;
}
