MMBytes/MultiGeiger-V2/main/lorawan.cpp

// LoRaWAN uplink for BOARD_HELTEC_WIFI_LORA32_V4_R2 — the tree's ONLY C++
// translation unit, kept behind the plain-C API in lorawan.h. Whole file is
// gated on CONFIG_GEIGER_LORAWAN (set only in that board's sdkconfig): the
// CMake SRCS conditional keeps it out of other boards' builds, and this
// guard additionally yields an empty TU for the cppcheck gate's other-board
// define sets (_build.cmd scans all of main/ for every board).
#include "sdkconfig.h"
#if CONFIG_GEIGER_LORAWAN

#include <string.h>
#include <time.h>
#include "freertos/FreeRTOS.h"
#include "freertos/task.h"
#include "freertos/queue.h"
#include "driver/gpio.h"
#include "driver/spi_master.h"
#include "esp_timer.h"
#include "esp_rom_sys.h"
#include "esp_log.h"
#include "nvs.h"
#include "RadioLib.h"

#include <sys/time.h>   // settimeofday() — DeviceTimeReq network time sync

extern "C" {
#include "hal.h"
#include "lorawan.h"
#include "lorawan_codec.h"
#include "config.h"
#include "applog.h"
#include "ntp.h"       // ntp_boot_epoch() — "has SNTP ever synced" gate for time sync
#include "version.h"   // VERSION_STR -> s_version_packed (lw_pack_version)
}

static const char *TAG = "lorawan";

// RadioLib HAL on raw IDF-6 drivers. CONFIG_FREERTOS_HZ stays 100: delay()
// is a hybrid — whole ticks via vTaskDelay (scheduler-friendly for the
// multi-second RX-window waits), sub-tick remainder busy-waited on esp_timer
// so LoRaWAN's ms-scale window timing holds without a global tick-rate bump.
//
// Reconciled against the fetched RadioLib 7.2.1 headers
// (managed_components/jgromes__radiolib/src/Hal.h): base-class constructor
// arity/order (input, output, low, high, rising, falling) and the full
// pure-virtual list match this class exactly — no adaptation needed.
class GeigerLoRaHal : public RadioLibHal {
public:
    GeigerLoRaHal()
        : RadioLibHal(GPIO_MODE_INPUT, GPIO_MODE_OUTPUT, 0, 1,
                      GPIO_INTR_POSEDGE, GPIO_INTR_NEGEDGE) {}
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
